squaresausage/Open-Source-PC110/optical/layers/README.md

## Layer Stack

BC2  -- Bottom Layer

BC1

IP2  -- Ground Layer

IC4

IC3

IC2

IC1

IP1 -- Power Layer

FC1

FC2 -- Top Layer

Link to high res pictures: https://drive.google.com/drive/folders/1oFIpbjULZVqb537QuhwhyOqd0YHSsCfh?usp=sharing
