squaresausage/Open-Source-PC110/PCB/Mainboard/README.md

### IBM PC110 PCB redesigned in KiCad

Layer Stack-up

| Index | Layer name | Description  |
| ----- | --- | --- |
| 1 | FC2 | Top |
| 2 | FC1 | Signal |
| 3 | IP1 | Power |
| 4 | IC1 | Signal |
| 5 | IC2 | Signal |
| 6 | IC3 | Signal |
| 7 | IC4 | Signal |
| 8 | IP2 | Ground |
| 9 | BC1 | Signal |
| 10 | BC2 | Bottom |

Here is a render of FC1, IC1, IC2, IC3, IC4 and BC1 together:

Screenshot 2025-01-25 at 10 13 16 PM

And here is a render of FC2, FC1, IC1, IC2, IC3, IC4, BC1 and BC2 together:
Screenshot 2025-02-05 at 3 54 23 PM

And here are 3D renders from the top and bottom layers:

Top side:

Real picture:



3D render:

Screenshot 2025-03-01 at 7 24 52 AM

Bottom side:

Real picture:



3D render:

Screenshot 2025-03-01 at 8 22 09 AM

Schematic Organization
-----
Here is a view of the schematic hierarchy:

Screenshot 2025-06-28 at 11 49 18 PM

Description of each schematic sheet

| Page | Sheet Name | Description  |
| ---- | --- | --- |
| 1 | Root | Index of all sheets  |
| 2 | Clock | Local Oscillator and Clock Distribution Tree |
| 3 | Processor  | CPU and Debug pins |
| 4 | Chipset  | SCAMP IV chipset North Bridge |
| 5 | VGA | Video Controller and Video RAM |
| 6 | Memory  | Internal Memory Back and RAM Expansion Connector |
| 7 | ROM | BIOS and Font Maskrom |
| 8 | ASIC | Bowman and Pluto, South Bridge |
| 9 | Super IO | FDD, Parallel and Serial ports |
| 10 | Power | Power Controller, PSU Connector, Status LCD, and Touchpad |
| 11 | PCMICA  | PCMCIA Controller and Related Power Controller |
| 12 | Audio | Sound Controller, FM Synthesizer and related analogue AMP |
| 13 | Storage | Internal Flash memory, CF card interface |
| 14 | Keyboard | Keyboard controller, Trackpoint controller |
| 15 | Docking | Docking Station, Internal Modem Connector |

Combined Schematic on one page
-----
Here is a combined schematic on a single page, just for the appreciation of its complexity.

PC110-Singlesheet-Schematic

Aside from the fun aspect of combining all the sheets on a single one, there is a practical use that is related to the recreation of the schematic from a given PCB. On KiCad, you cannot select components from different sheets simultaneously. Therefore, you cannot highlight all the components on your schematic at once to see if there is still any component on the layout that is not mapped. However, with a single sheet compilation, you can do that (as it is shown below) and you can go back to the layout and see if there is still any component that is left behind. Below you can see that, on the layout for both top and bottom layers, all the components are highlighted.

All components selected on the schematic

Screenshot 2025-07-19 at 1 20 59 PM

Highlighted components on the top layer



Highlighted components on the bottom layer



And here is the SVG version of the single-sheet 

PC110-Singlesheet-Schematic

PCB statistics report
=====================

Board
-----
- Width: 150.0500 mm
- Height: 107.3513 mm
- Area: 12400.2967 mm²

Pads
----
- Through hole: 29
- SMD: 4860
- Total: 4889

Vias
----
- Through vias: 2407
- Blind/buried: 3684
- Total: 6091

Components
----------

| | Front Side | Back Side | Total |
|---|---|---|---|
|THT: | 1 | 0 | 1 |
|SMD: | 486 | 446 | 932 |
|Unspecified:  | 0 | 1 | 1 |
|Total: | 487 | 447 | 934 |

Drill holes
-----------

| Count | Shape | X Size | Y Size | Plated | Via/Pad | Start Layer | Stop Layer |
|---|---|---|---|---|---|---|---|
|  1950 | Round | 0.2000 mm | 0.2000 mm | PTH | Via | BC1 | BC2 |
|  1914 | Round | 0.2000 mm | 0.2000 mm | PTH | Via | FC2 | BC2 |
|  1730 | Round | 0.2000 mm | 0.2000 mm | PTH | Via | FC2 | FC1 |
| 493 | Round | 0.3000 mm | 0.3000 mm | PTH | Via | FC2 | BC2 |
| 20 | Round | 0.8000 mm | 0.8000 mm | PTH | Pad | FC2 | BC2 |
| 5 | Round | 1.0000 mm | 1.0000 mm | PTH | Pad | FC2 | BC2 |
| 2 |  Slot | 2.0000 mm | 0.9000 mm | PTH | Pad | FC2 | BC2 |
| 2 |  Slot | 0.8000 mm | 2.2000 mm | PTH | Pad | FC2 | BC2 |
| 2 | Round | 0.2000 mm | 0.2000 mm | PTH | Via | FC2 | IC2 |
| 1 | Round | 0.2000 mm | 0.2000 mm | PTH | Via | FC2 | IC1 |
| 1 | Round | 0.3000 mm | 0.3000 mm | PTH | Via | BC1 | BC2 |
| 1 | Round | 0.2000 mm | 0.2000 mm | PTH | Via | IP1 | BC2 |

Here is a cross section of the PCB stack-up

Board_cross_section
