squaresausage/Open-Source-PC110/Modifications/Altium/README.md

Here you can find the PCB projects converted from KiCad to Altium to bring more versatility and make Altium's special offerings available to this project.
