squaresausage/Open-Source-PC110/Modifications/PC110-ITX-all-in-one/README.md

## PC110-ITX all-in-one

This is an effort to build an ITX form factor motherboard with all the PC110 components, the docking station as the PSU board all blended.
