squaresausage/Open-Source-PC110/Modifications/PC110-ITX/README.md

## PC110-ITX Form Factor

This is an effort to build an ITX form factor motherboard with all the PC110 components, but the BGA parts have been converted to QFP alternatives.

Here is how the netlist looked before the placement.

Screenshot 2025-07-03 at 5 40 27 PM

And here is when the placement has been performed.

Screenshot 2025-07-03 at 6 51 45 PM

Also, here is a 3D render of the board.

Screenshot 2025-07-03 at 6 53 05 PM
