squaresausage/Open-Source-PC110/Modifications/RAS4/README.md

## Using RAS4 to add extra 4MB to the internal RAM

VL_D12 is now labled as RAS#4 on the schematic

Screenshot 2025-06-20 at 5 41 18 AM

Screenshot 2025-06-20 at 5 41 07 AM
