squaresausage/Open-Source-PC110/PCB/RAM-16MB/README.md

## 16MB RAM Module PCB

Layer Stack-up

| Index | Layer name | Description  |
| ----- | --- | --- |
| 1 | FC | Top |
| 2 | IP1 | Power |
| 3 | IP2 | Ground |
| 4 | BC | Bottom |

Here is a rendering of FC, IP1, IP2 and BC:

Screenshot 2025-03-25 at 2 49 15 AM

Here are renderings of the 3D model of the Docking Station PCB

Screenshot 2025-03-26 at 7 45 36 PM

Screenshot 2025-03-26 at 7 45 54 PM

PCB statistics report
=====================
- Date: Tuesday, March 25, 2025 at 03:06:19 AM
- Project: RAM-Module
- Board name: RAM-Module

Board
-----
- Width: 41.4600 mm
- Height: 41.6000 mm
- Area: 1724.3156 mm²
- Thickness: 0.6mm

Pads
----
- Through hole: 0
- SMD: 312
- Connector: 0
- NPTH: 0

Vias
----
- Through vias: 152
- Blind/buried: 0
- Micro vias: 0

Components
----------

| | Front Side | Back Side | Total |
|---|---|---|---|
|THT: | 0 | 0 | 0 |
|SMD: | 17 | 4 | 21 |
|Unspecified:  | 0 | 1 | 1 |
|Total: | 17 | 5 | 22 |

Drill holes
-----------

| Count | Shape | X Size | Y Size | Plated | Via/Pad | Start Layer | Stop Layer |
|---|---|---|---|---|---|---|---|
| 152 | Round | 0.3000 mm | 0.3000 mm | PTH | Via | FC | BC |
