squaresausage/Open-Source-PC110/PCB/Modem/README.md

## Here is the PCB Layout for the Modem Board

Layer Stack-up

| Index | Layer name | Description  |
| ----- | --- | --- |
| 1 | FC | Top |
| 2 | IC1 | Signal |
| 4 | IP1 | Power |
| 3 | IP2 | Power |
| 4 | IC2 | Signal |
| 4 | BC | Bottom |

Here is a render of FC, IC1, IP1, IP2, IC2 and BC:

Screenshot 2025-03-21 at 8 33 39 PM

Here are the 3D renders from the board:

Screenshot 2025-03-21 at 8 27 20 PM

Screenshot 2025-03-25 at 2 58 01 AM

PCB statistics report
=====================
- Date: Friday, March 21, 2025 at 08:35:15 PM
- Project: Modem
- Board name: Modem

Board
-----
- Width: 64.6100 mm
- Height: 58.9100 mm
- Area: 3494.8376 mm²

Pads
----
- Through hole: 23
- SMD: 735
- Connector: 0
- NPTH: 0

Vias
----
- Through vias: 344
- Blind/buried: 0
- Micro vias: 0

Components
----------

| | Front Side | Back Side | Total |
|---|---|---|---|
|THT: | 0 | 0 | 0 |
|SMD: | 75 | 136 | 211 |
|Unspecified:  | 0 | 0 | 0 |
|Total: | 75 | 136 | 211 |

Drill holes
-----------

| Count | Shape | X Size | Y Size | Plated | Via/Pad | Start Layer | Stop Layer |
|---|---|---|---|---|---|---|---|
| 344 | Round | 0.3000 mm | 0.3000 mm | PTH | Via | FC | BC |
| 18 | Round | 1.0000 mm | 1.0000 mm | PTH | Pad | FC | BC |
| 5 | Round | 1.2000 mm | 1.2000 mm | PTH | Pad | FC | BC |
