squaresausage/Open-Source-PC110/Flash/EN29F040A/README.md

## Flash dump from the EN29FF040A from the Modem board
