squaresausage/Open-Source-PC110/PCB/DockingStation/README.md

## Docking Station PCB

Layer Stack-up

| Index | Layer name | Description  |
| ----- | --- | --- |
| 1 | FC | Top |
| 2 | IP1 | Ground |
| 3 | IP2 | Power |
| 4 | BC | Bottom |

Here is a rendering of FC, IP1, IP2 and BC:

Screenshot 2025-03-18 at 2 07 06 PM

Here are renderings of the 3D model of the Docking Station PCB

Screenshot 2025-03-18 at 2 07 46 PM

Screenshot 2025-03-18 at 2 08 01 PM
