squaresausage/Open-Source-PC110/PCB/PSU/README.md

## Here is the PCB Layout for the PSU board

Layer Stack-up

| Index | Layer name | Description  |
| ----- | --- | --- |
| 1 | FC | Top |
| 2 | IC | Signal |
| 3 | IP | Ground |
| 4 | BC | Bottom |

Here is a render of FC, IC, IP and BC:

Screenshot 2025-03-15 at 6 35 28 PM

Here are 3D models of the PSU board:

Screenshot 2025-03-15 at 6 34 14 PM

Screenshot 2025-03-15 at 6 34 32 PM

PCB statistics report
=====================
- Date: Saturday, March 15, 2025 at 01:16:45 PM
- Project: PSU
- Board name: PSU

Board
-----
- Width: 72.3100 mm
- Height: 44.9600 mm
- Area: 2701.6649 mm²

Pads
----
- Through hole: 20
- SMD: 688
- Connector: 0
- NPTH: 0

Vias
----
- Through vias: 212
- Blind/buried: 0
- Micro vias: 0

Components
----------

| | Front Side | Back Side | Total |
|---|---|---|---|
|THT: | 0 | 10 | 10 |
|SMD: | 171 | 76 | 247 |
|Unspecified:  | 1 | 0 | 1 |
|Total: | 172 | 86 | 258 |

Drill holes
-----------

| Count | Shape | X Size | Y Size | Plated | Via/Pad | Start Layer | Stop Layer |
|---|---|---|---|---|---|---|---|
| 203 | Round | 0.3000 mm | 0.3000 mm | PTH | Via | FC | BC |
| 14 | Round | 0.8000 mm | 0.8000 mm | PTH | Pad | FC | BC |
| 6 | Round | 1.3000 mm | 1.3000 mm | PTH | Pad | FC | BC |
| 5 | Round | 0.8000 mm | 0.8000 mm | PTH | Via | FC | BC |
| 3 | Round | 0.6000 mm | 0.6000 mm | PTH | Via | FC | BC |
| 1 | Round | 1.0000 mm | 1.0000 mm | PTH | Via | FC | BC |
