squaresausage/Open-Source-PC110/Flash/OKI-MSM538032E/README.md

## OKI MSM538032E Memory dump

Here is a memory dump from the MSM538032E made by OKI.

You can use https://binvis.io/ to study the binary file.
In this analysis https://github.com/bbbradsmith/binxelview was used.

Here is how the chip was fitted on a proto board to be read by a programmer





And here are the results



It looks like the first 8k bytes are exposed in the "font window" and is a properly formatted option rom with the Japanese character sets.



This is what the 8k bytes look like:

WhatsApp Image 2025-03-04 at 20 44 57

Higher resolution character sets in their too.

Digging further in the code it seems that there is a reference to the different size character sets:
