squaresausage/Open-Source-PC110/datasheets/top/README.md

## parts on the top layer

tiplane
tiplane-1
