squaresausage/Open-Source-PC110/datasheets/bottom/README.md

## parts on the bottom later
teplane
teplane-1
