squaresausage/Open-Source-PC110/PCB/Mainboard/Single-Sheet-Schematic/README.md

Single Sheet Schematic

All the sheets were compiled into a single sheet
