squaresausage/Open-Source-PC110/PCB/Keyboard/Membrane/README.md

## IBM PC110 Keyboard Membrane

## Here is the PCB Layout for the PSU board

Layer Stack-up

| Index | Layer name | Description  |
| ----- | --- | --- |
| 1 | FC | Top |
| 1 | BC | Bottom |

Here is a render of FC and BC:

Screenshot 2025-03-25 at 11 03 26 PM

Here are 3D models of the Keyboard membrane:

Screenshot 2025-03-25 at 11 03 48 PM

Screenshot 2025-03-26 at 6 59 02 PM

These design files can be used to recreate the membrane from FlexPCB.
Additionally, their original membrane has been made using PET technology.
It can be built using PET technology. Here is an example of a vendor providing PET manufacturing service: 
https://www.pcbway.com/blog/Flexible_PCB/PET_7348f015.html
