squaresausage/Open-Source-PC110/datasheets/bottom/28F002 pinout.png

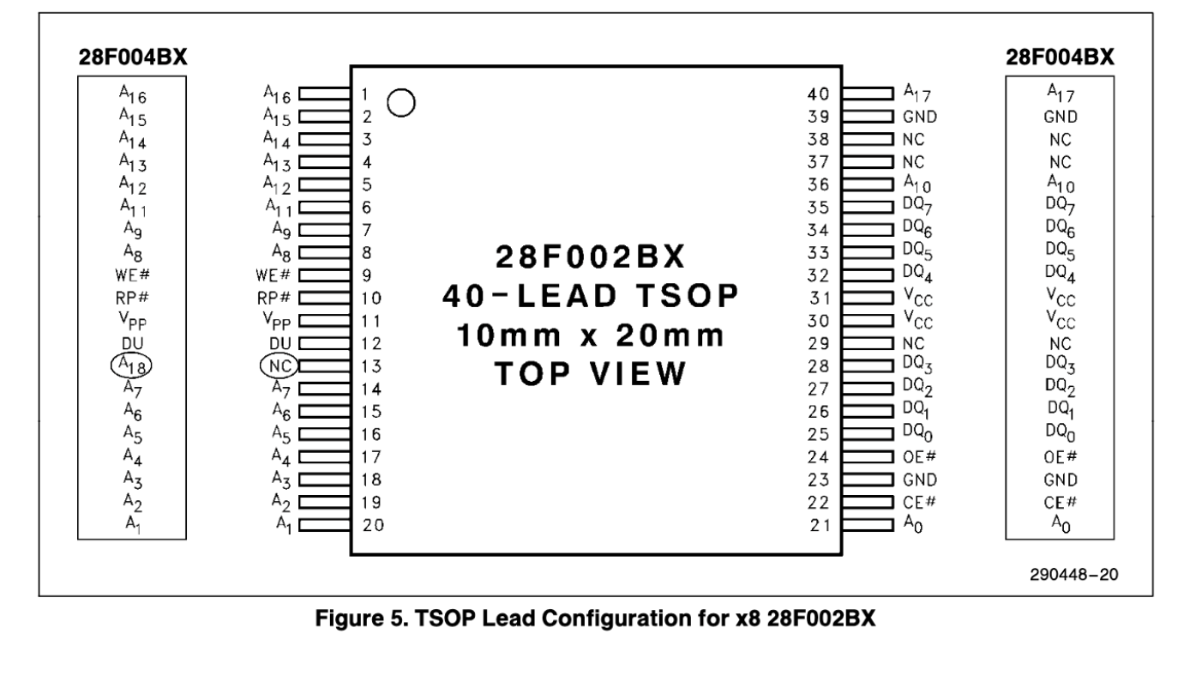
datasheets/bottom/28F002 pinout.png
