squaresausage/Open-Source-PC110/datasheets/bottom/AV9 pinout.png

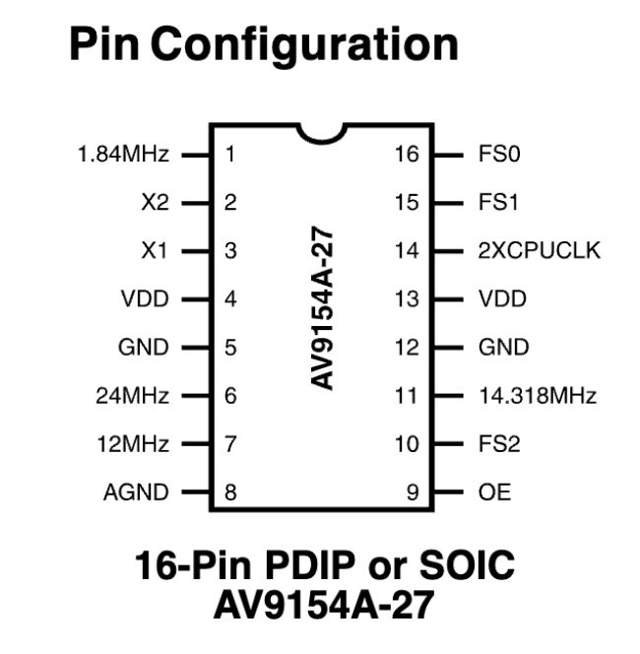
datasheets/bottom/AV9 pinout.png
