squaresausage/Open-Source-PC110/datasheets/bottom/D17137 pinout.png

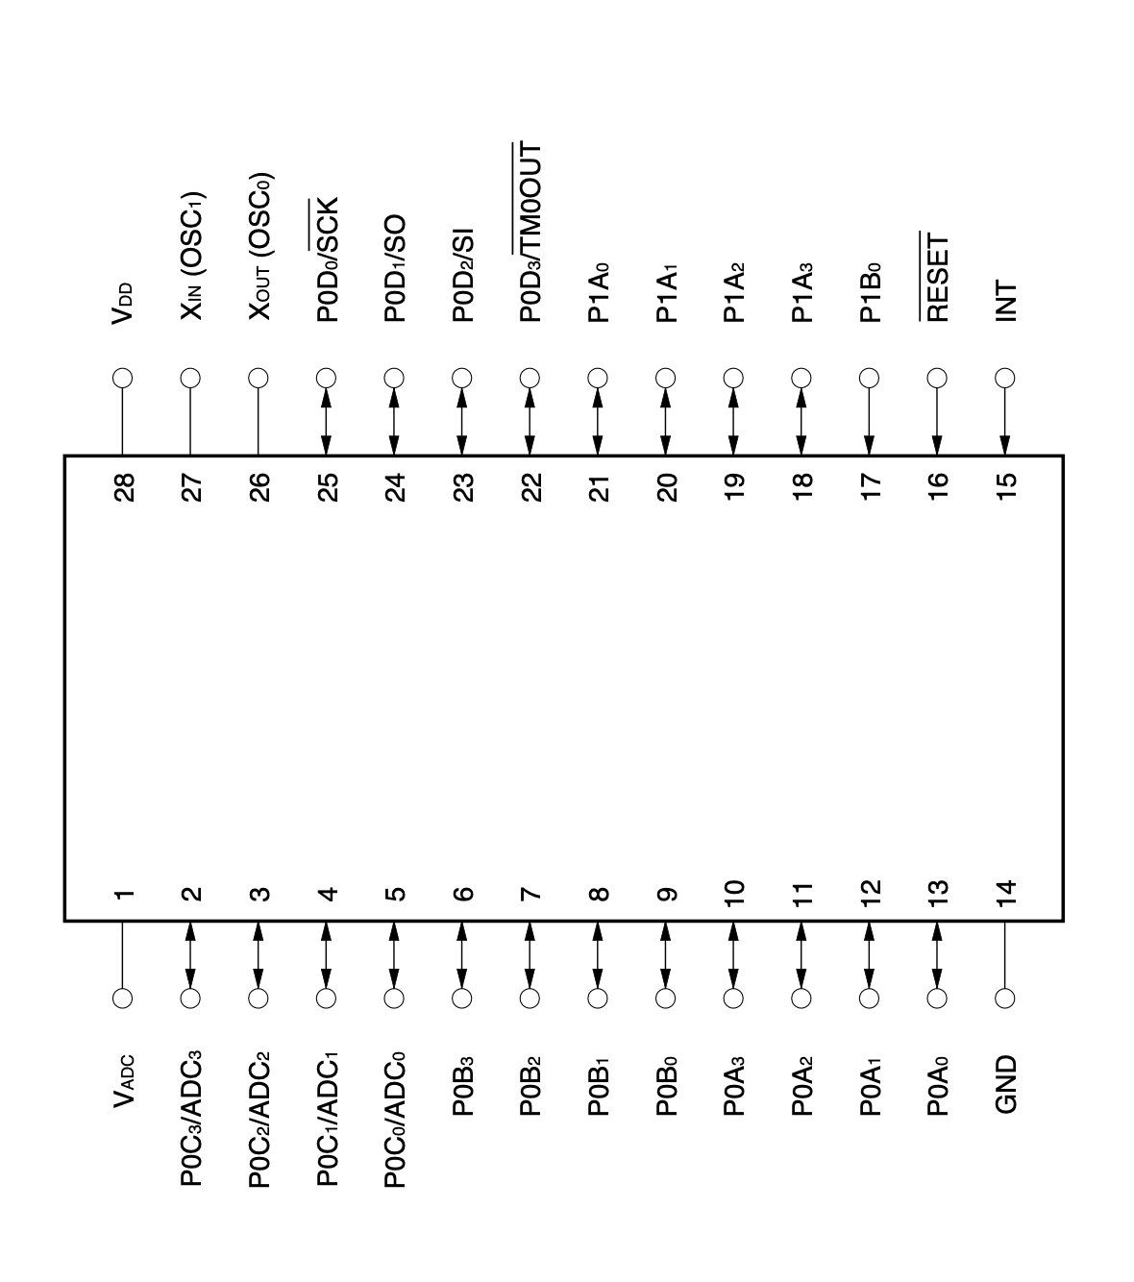
datasheets/bottom/D17137 pinout.png
