squaresausage/Open-Source-PC110/datasheets/bottom/F65535 BGA Ballmap.png

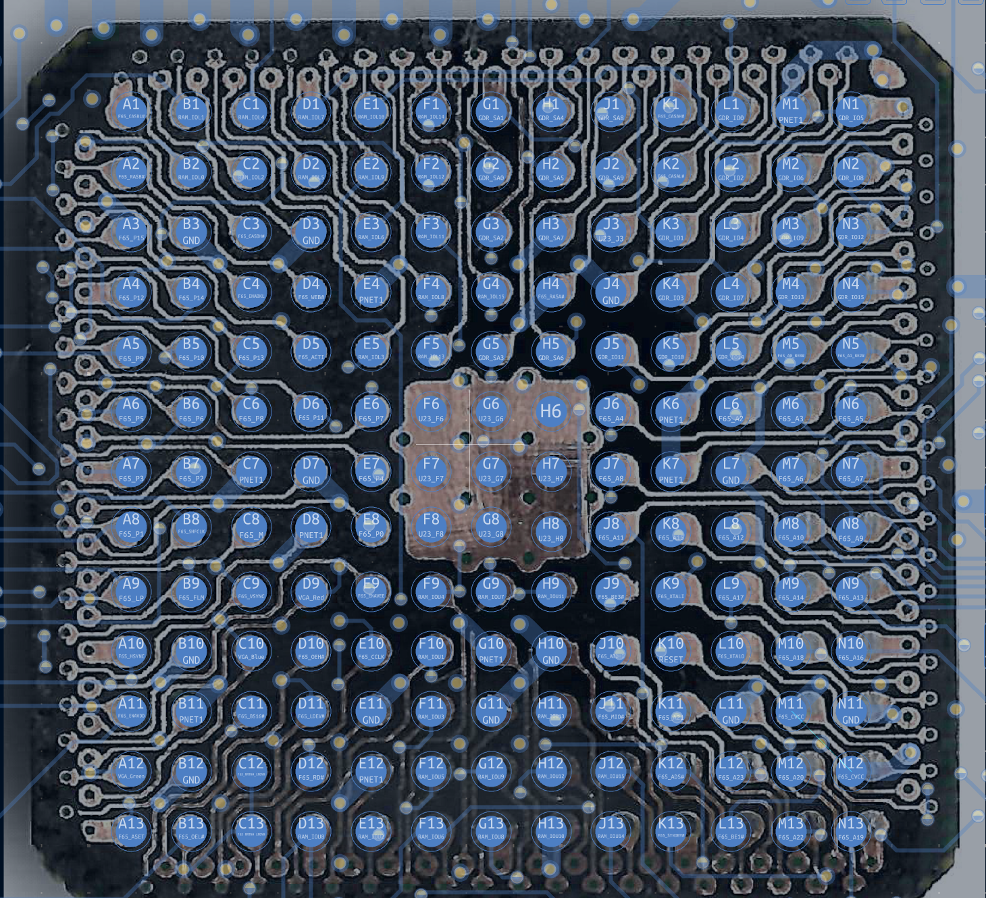
datasheets/bottom/F65535 BGA Ballmap.png
