squaresausage/Open-Source-PC110/datasheets/bottom/i486sx BGA ball map.png

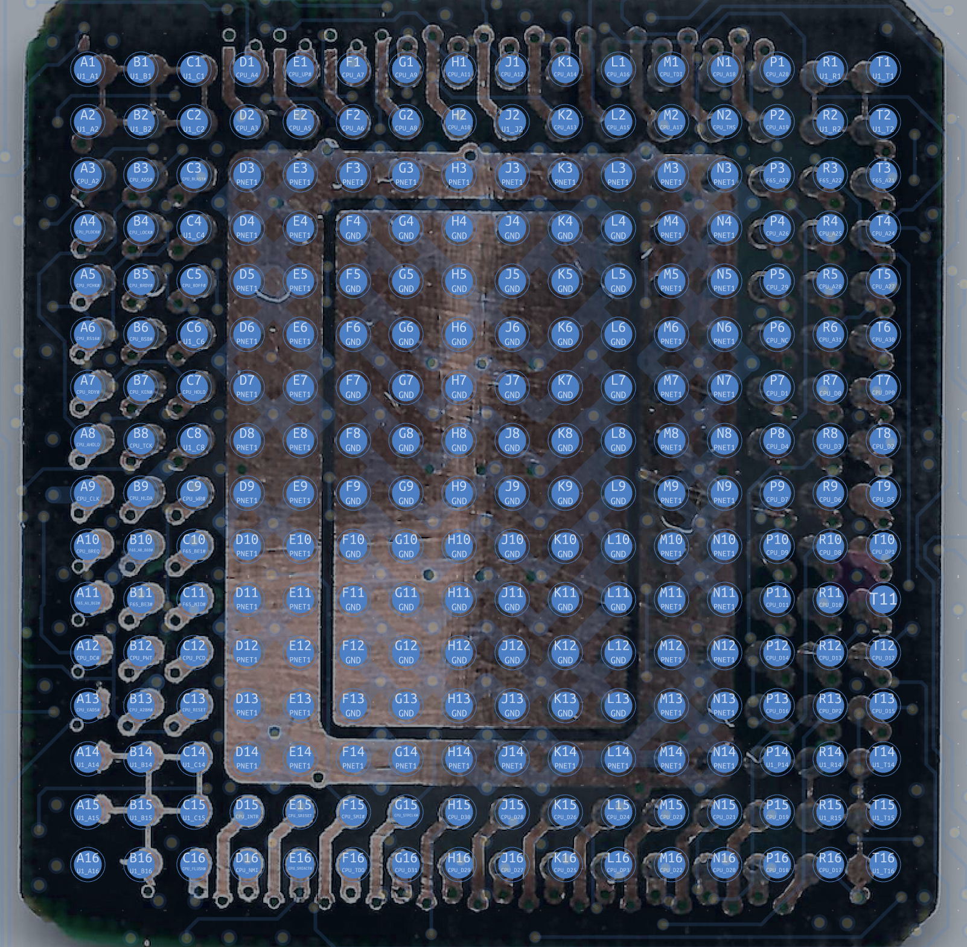
datasheets/bottom/i486sx BGA ball map.png
