squaresausage/Open-Source-PC110/datasheets/generic/connectors.jpg

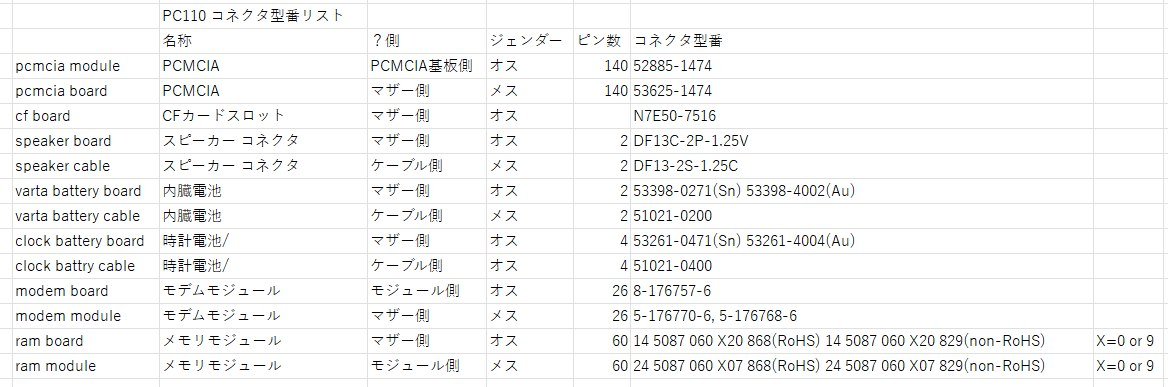
datasheets/generic/connectors.jpg
