squaresausage/Open-Source-PC110/datasheets/Modem/MN195001-pins.png

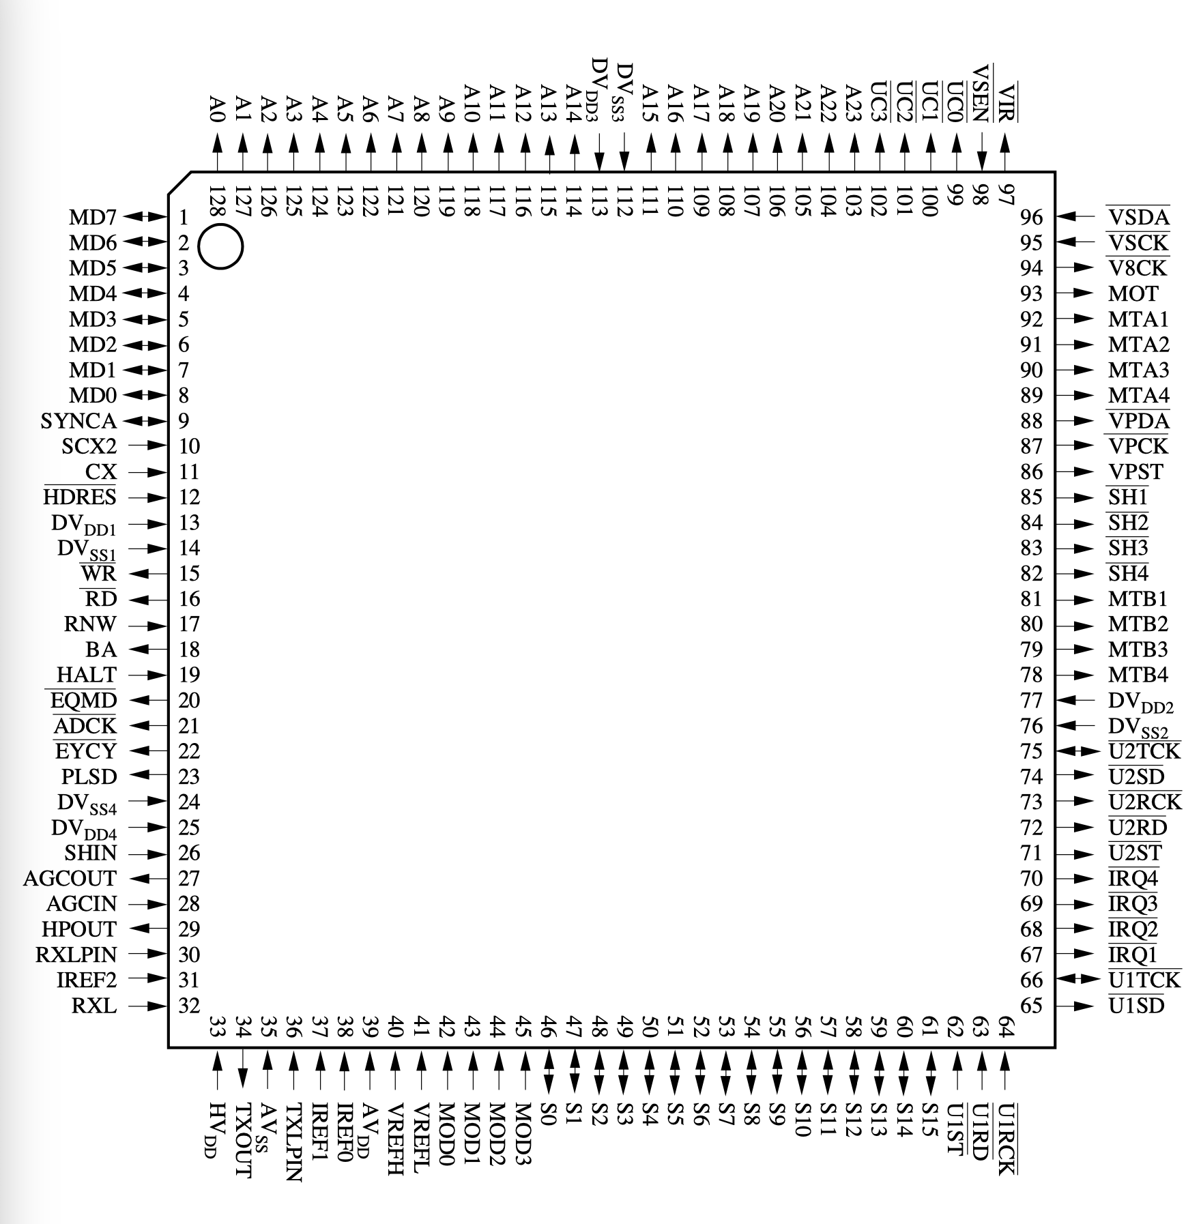
datasheets/Modem/MN195001-pins.png
