squaresausage/Open-Source-PC110/datasheets/top/15-m38.png

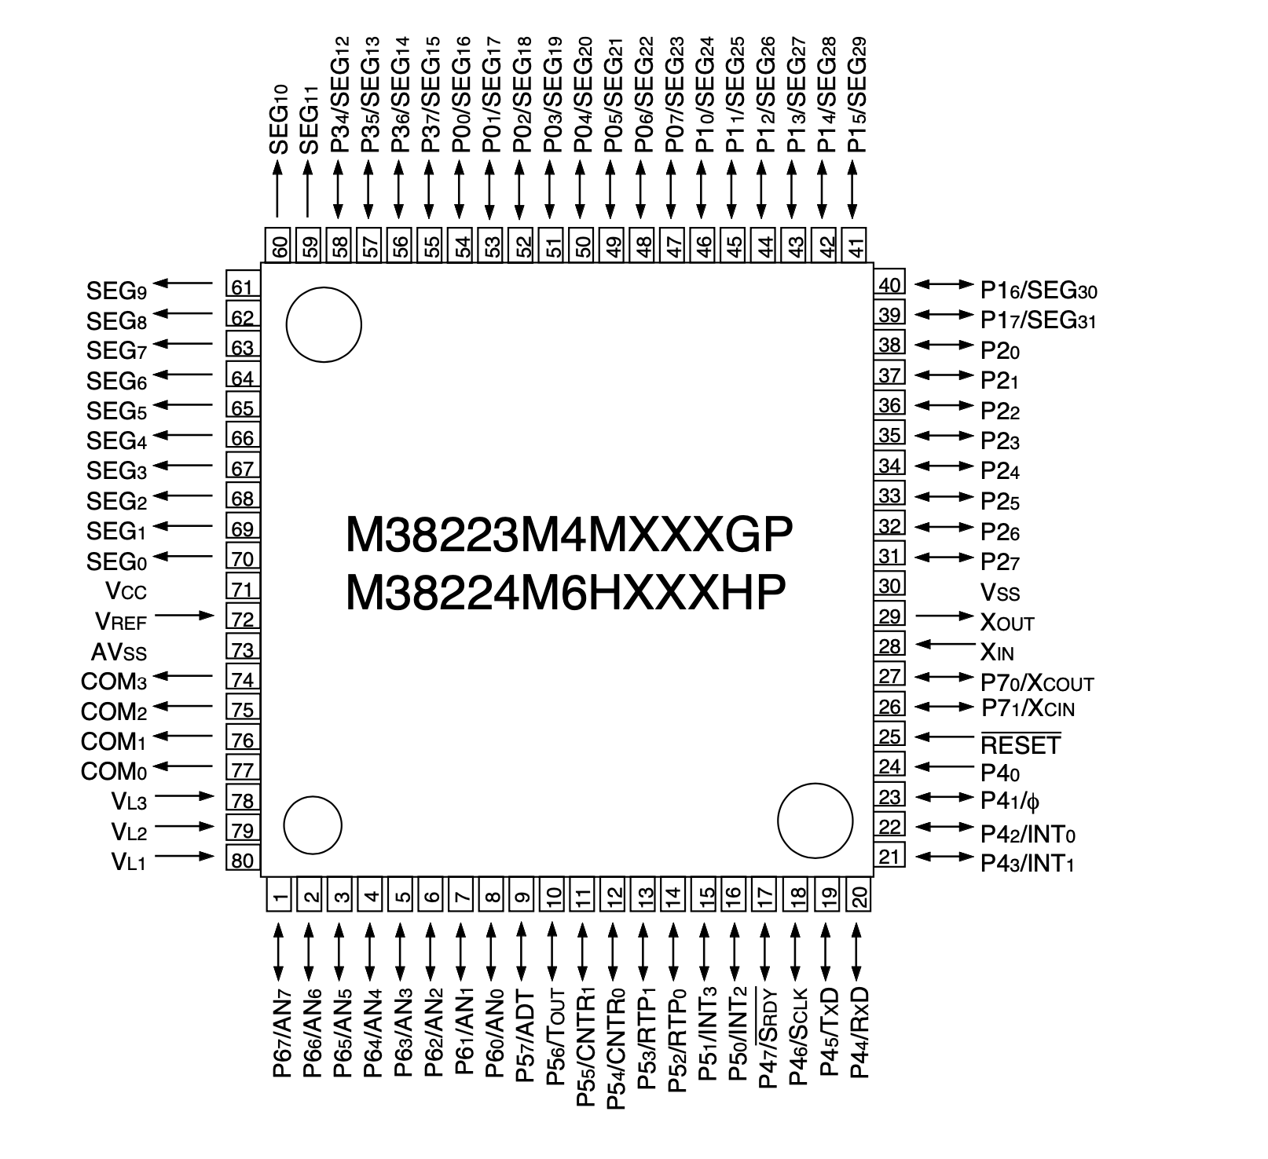
datasheets/top/15-m38.png
