squaresausage/Open-Source-PC110/datasheets/top/51w16160 pinout.png

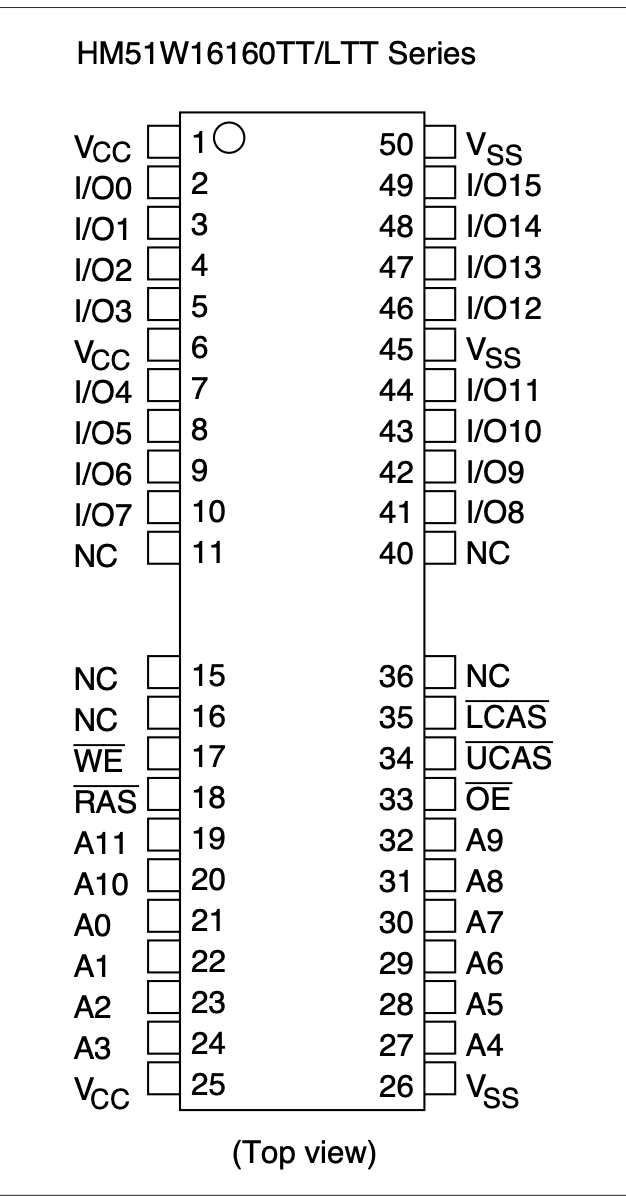
datasheets/top/51w16160 pinout.png
