squaresausage/Open-Source-PC110/datasheets/top/docking connector part.png

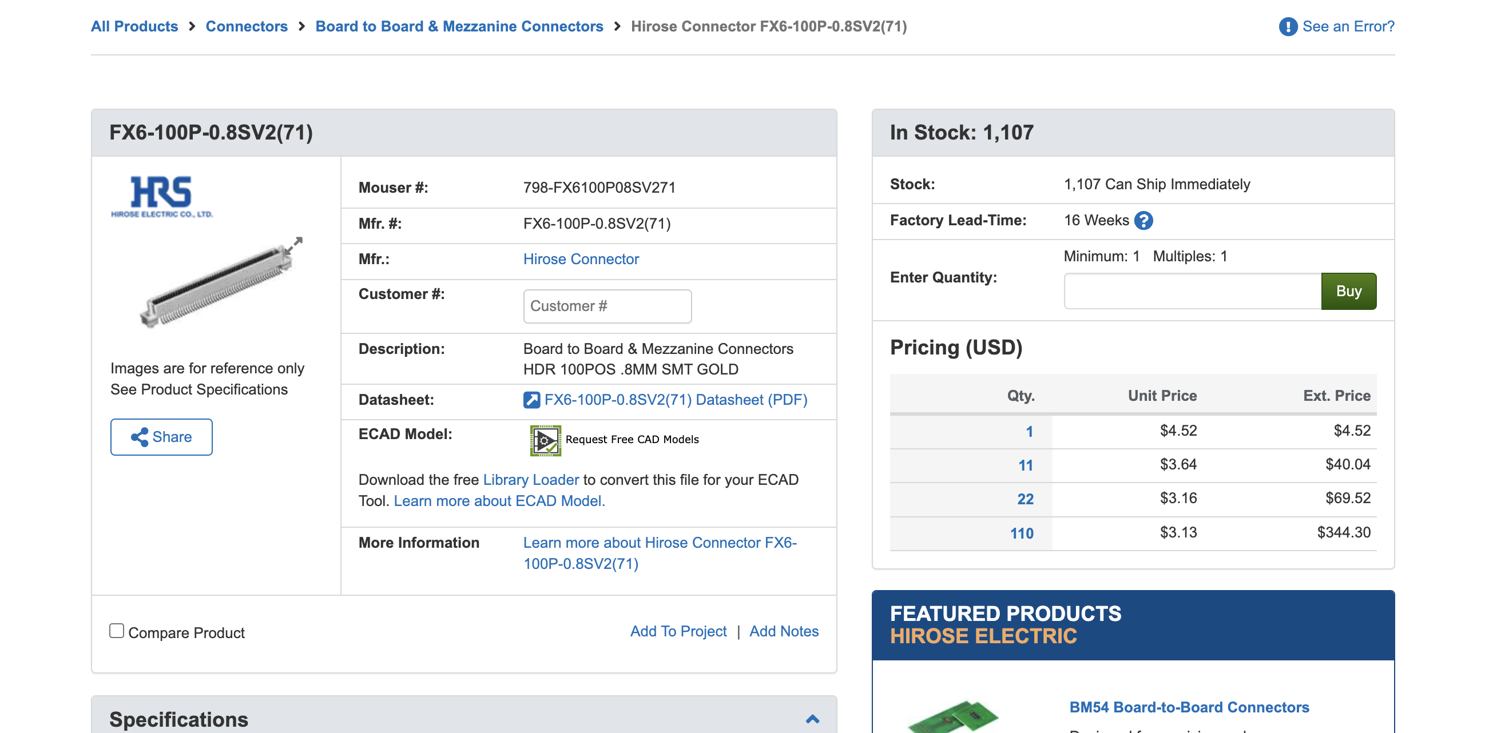
datasheets/top/docking connector part.png
