squaresausage/Open-Source-PC110/datasheets/top/docking pinout.jpg

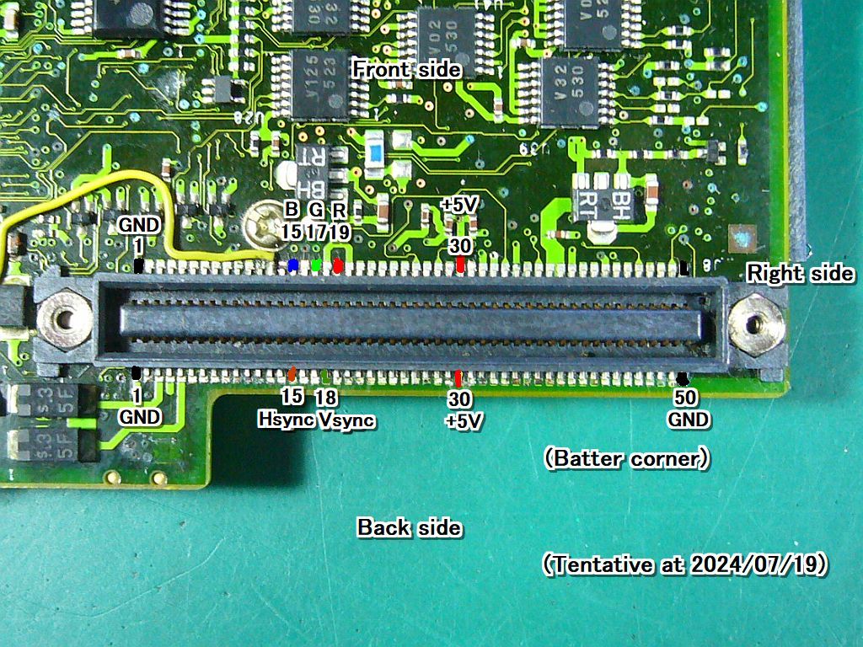
datasheets/top/docking pinout.jpg
