squaresausage/Open-Source-PC110/datasheets/top/LCD Connector.png

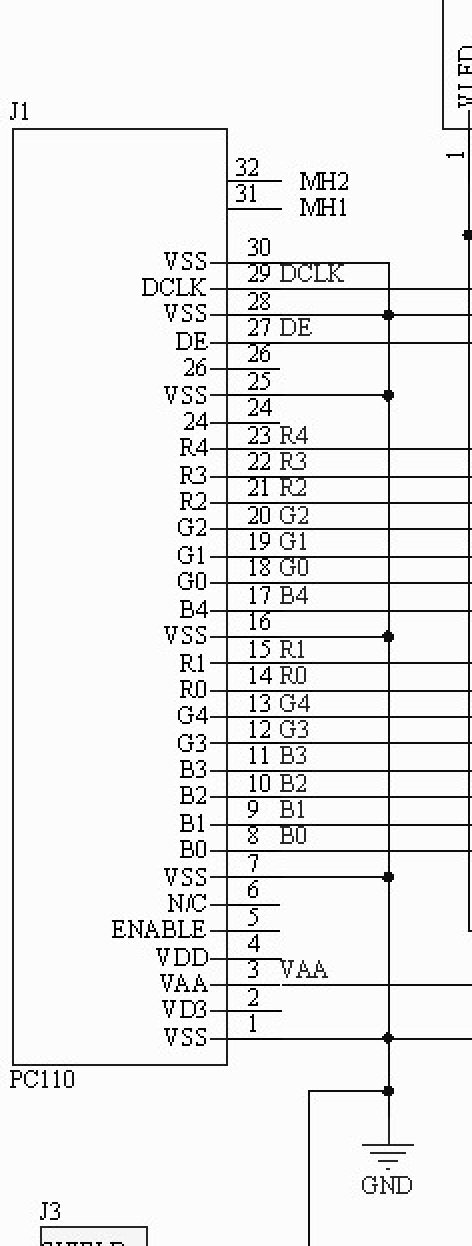
datasheets/top/LCD Connector.png
