squaresausage/Open-Source-PC110/datasheets/top/M538032C pinout.png

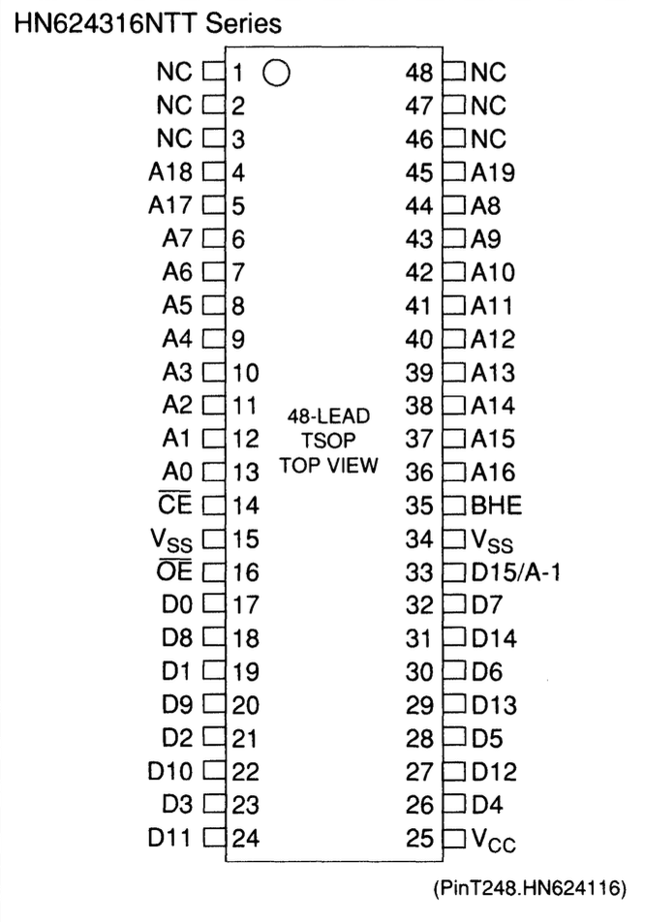
datasheets/top/M538032C pinout.png
