squaresausage/Open-Source-PC110/datasheets/top/MSM538032C pinout.png

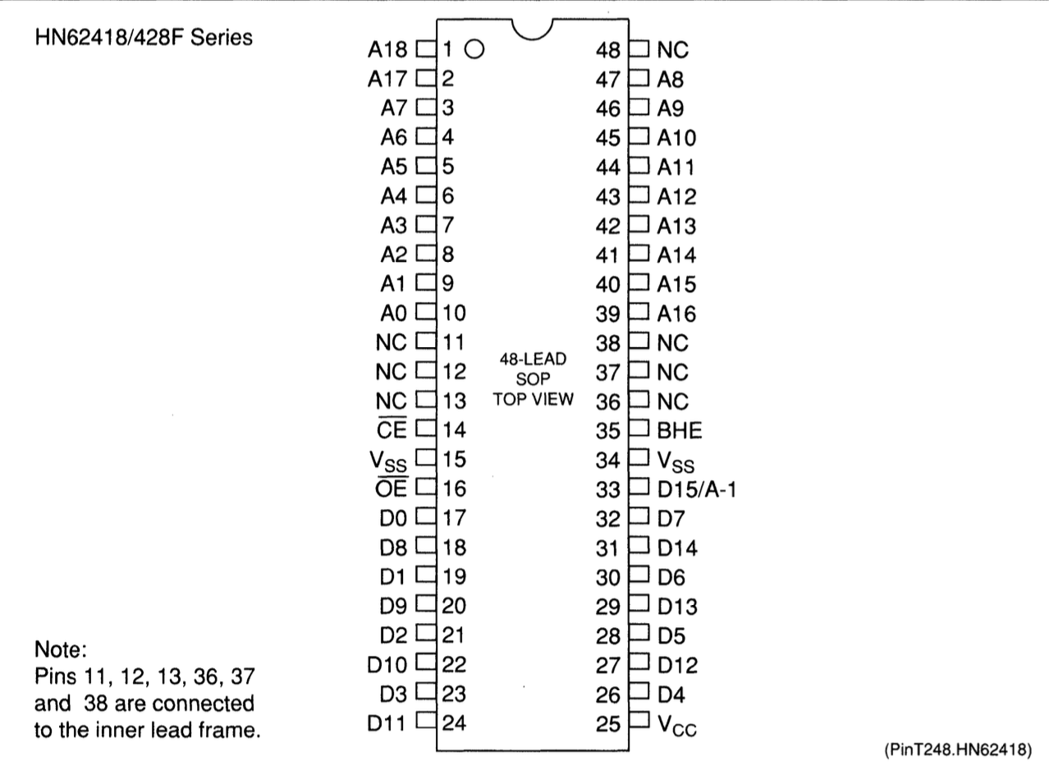
datasheets/top/MSM538032C pinout.png
