squaresausage/Open-Source-PC110/datasheets/top/power connector motherboard side part.png

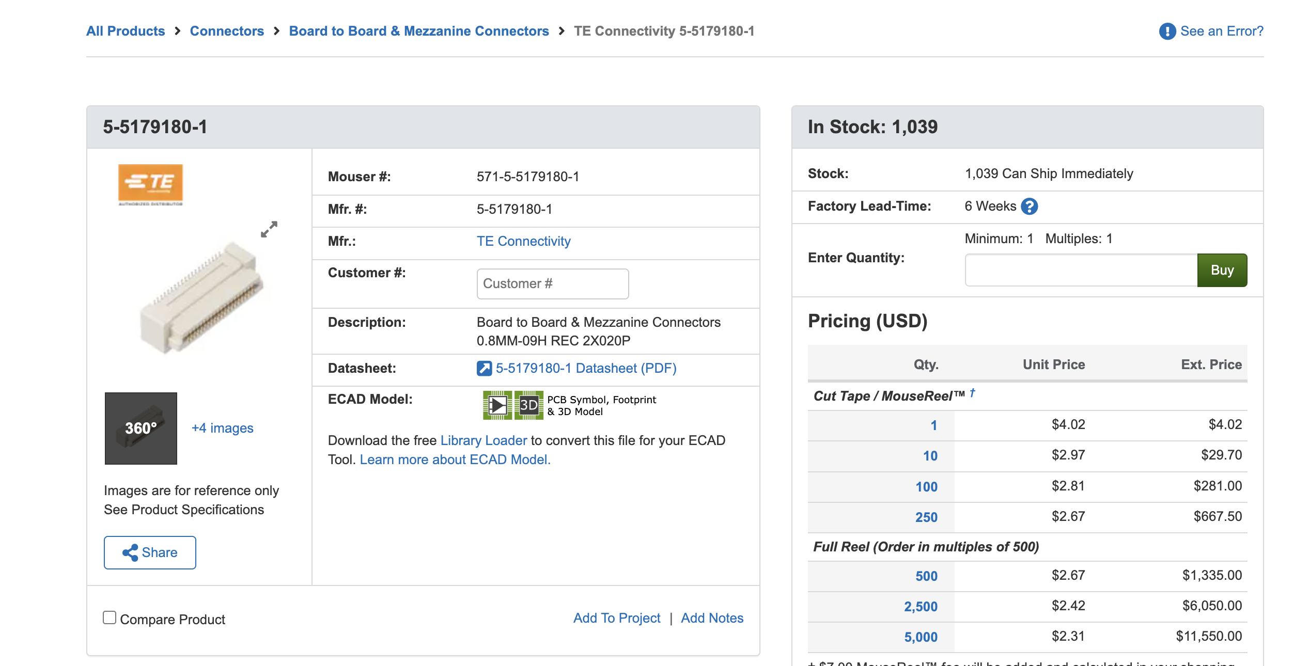
datasheets/top/power connector motherboard side part.png
