squaresausage/Open-Source-PC110/datasheets/top/power connector part.png

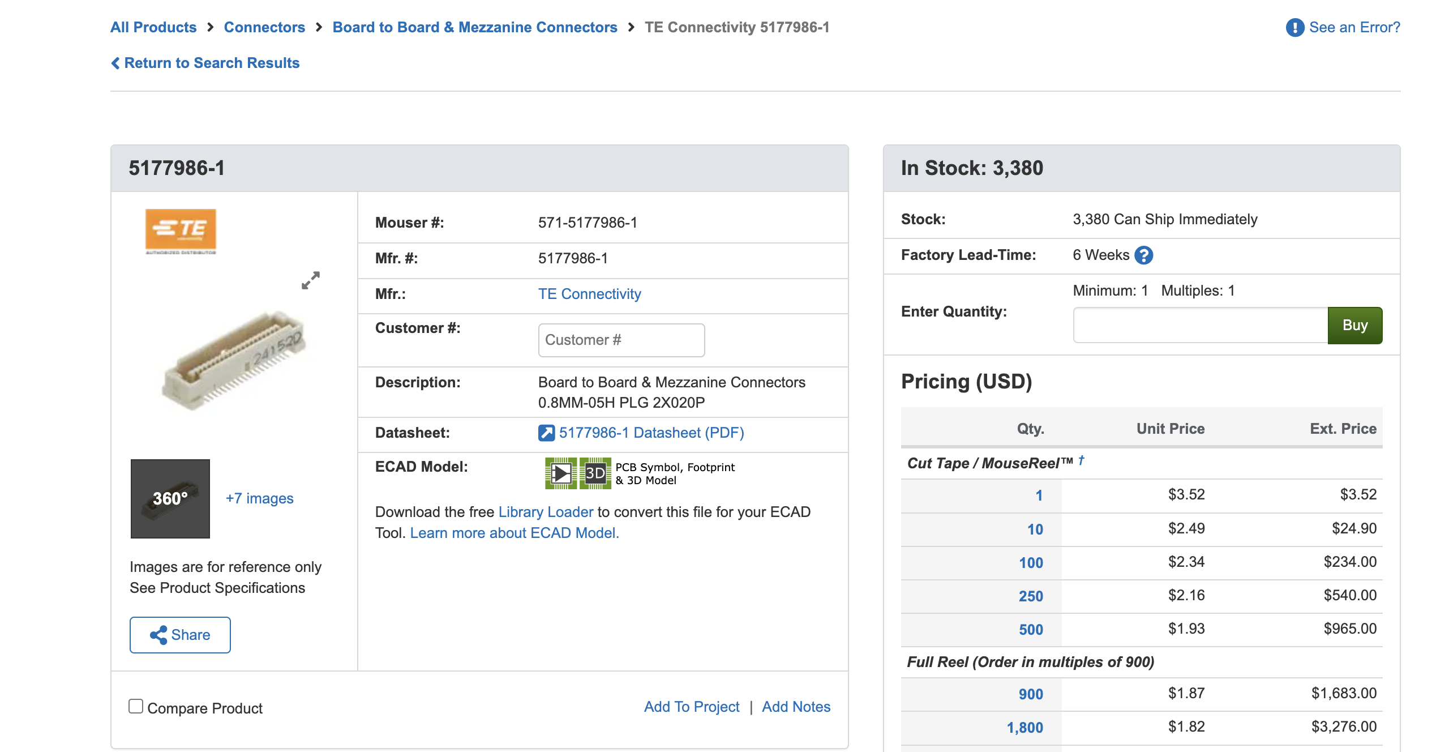
datasheets/top/power connector part.png
