squaresausage/Open-Source-PC110/datasheets/top/power connector.jpg

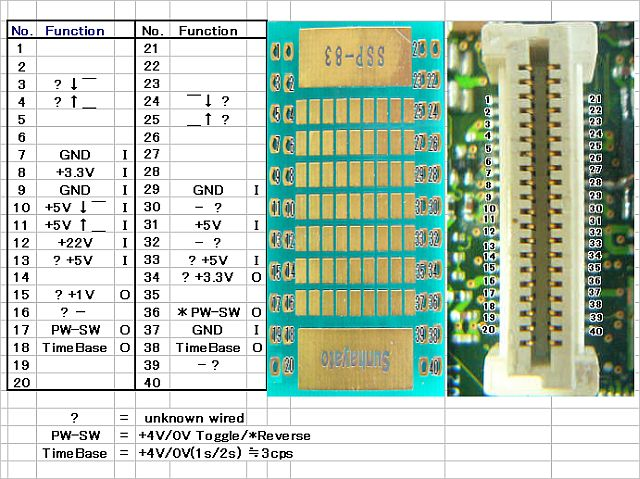
datasheets/top/power connector.jpg
