squaresausage/Open-Source-PC110/datasheets/top/RAM connector.jpg

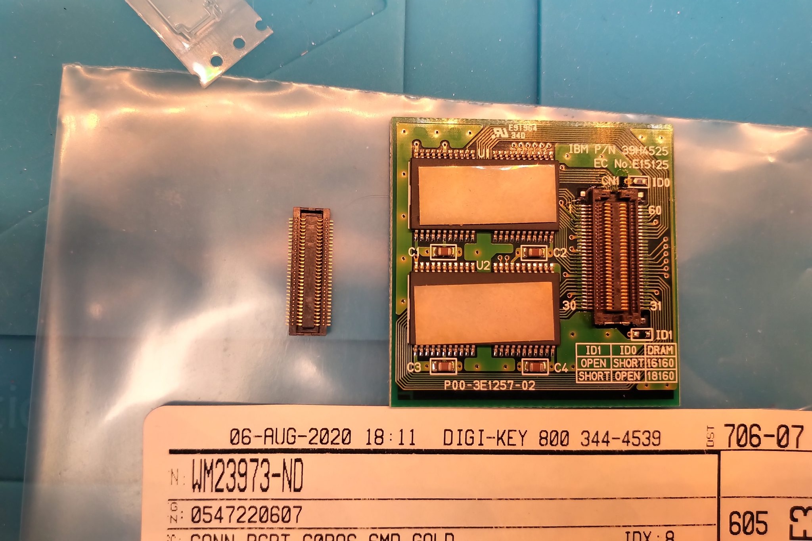
datasheets/top/RAM connector.jpg
