squaresausage/Open-Source-PC110/Modifications/RAS4/PHOTO-2025-06-20-01-07-58.jpg

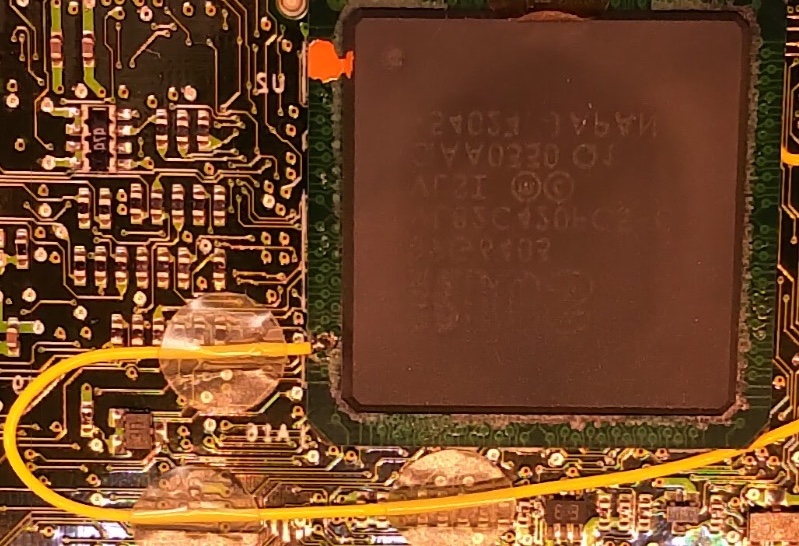
Modifications/RAS4/PHOTO-2025-06-20-01-07-58.jpg
