squaresausage/Open-Source-PC110/optical/16MB-RAM/back.jpeg

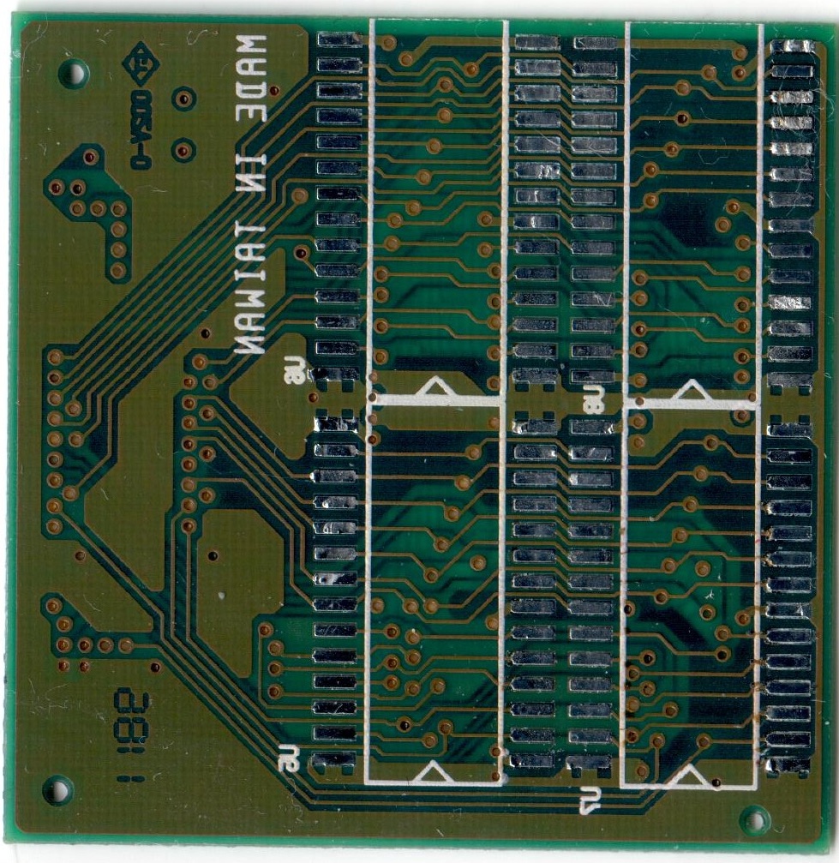
optical/16MB-RAM/back.jpeg
