squaresausage/Open-Source-PC110/optical/16MB-RAM/front.jpeg

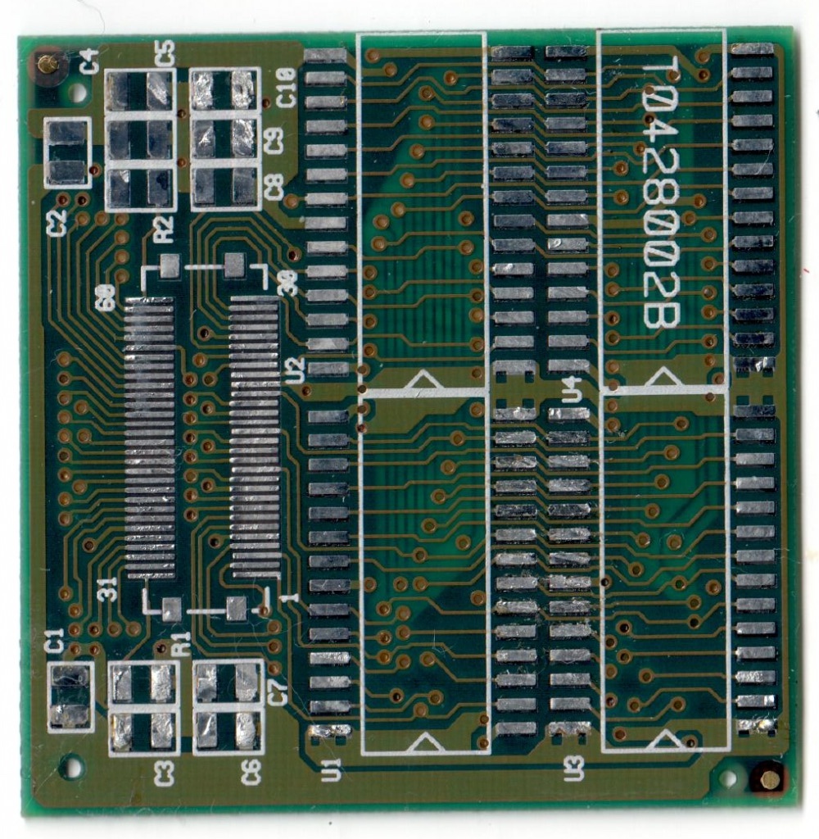
optical/16MB-RAM/front.jpeg
