squaresausage/Open-Source-PC110/optical/16MB-RAM/scan0001.jpg

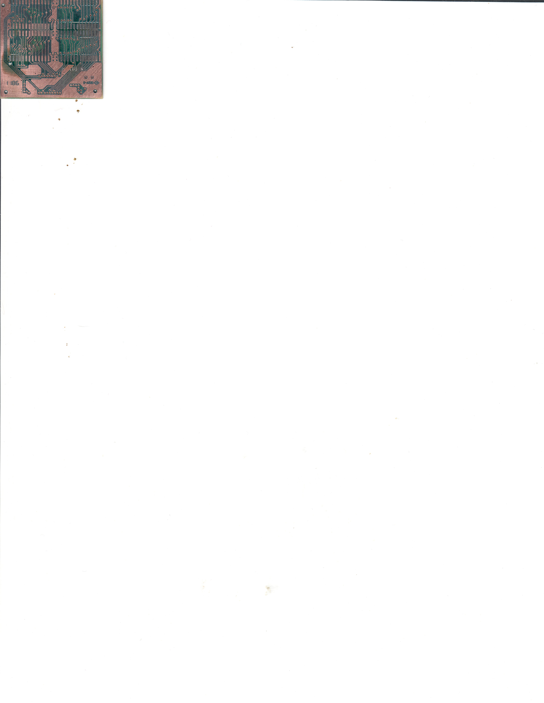
optical/16MB-RAM/scan0001.jpg
