squaresausage/Open-Source-PC110/optical/16MB-RAM/scan0003.jpg

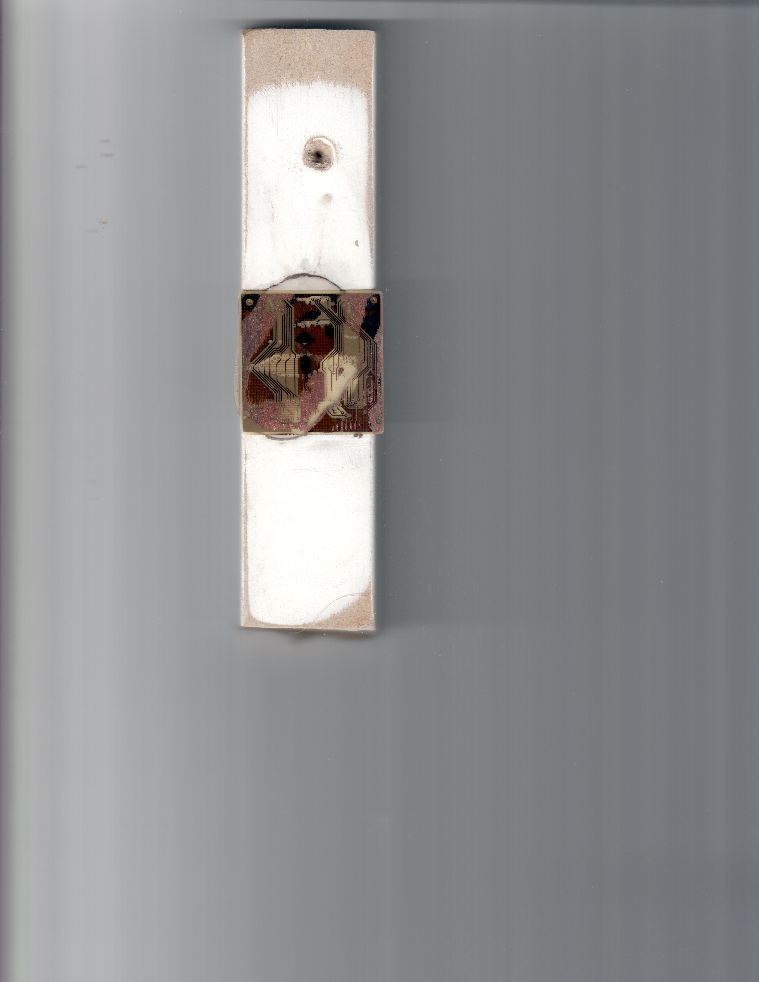
optical/16MB-RAM/scan0003.jpg
