squaresausage/Open-Source-PC110/optical/Chip Diagnostic/486sx BL.JPG

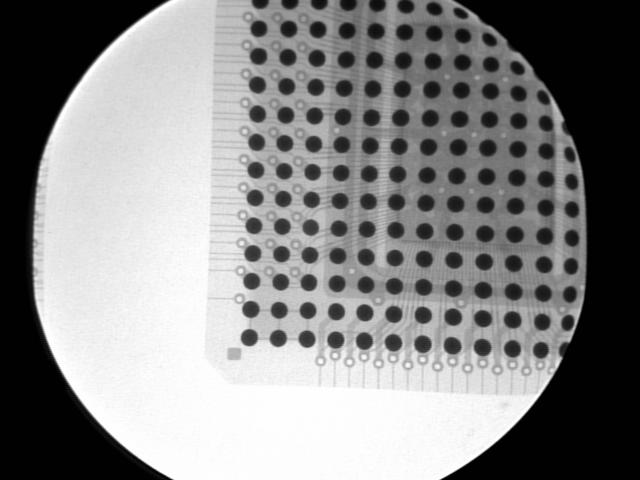
optical/Chip Diagnostic/486sx BL.JPG
