squaresausage/Open-Source-PC110/optical/Chip Diagnostic/486sx BR.JPG

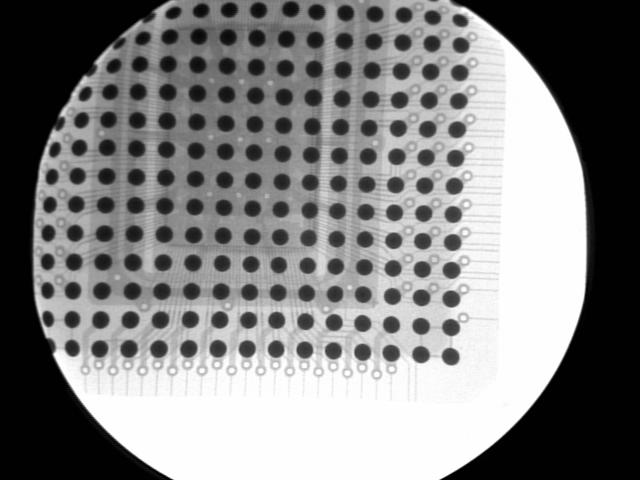
optical/Chip Diagnostic/486sx BR.JPG
