squaresausage/Open-Source-PC110/optical/Chip Diagnostic/486sx C.JPG

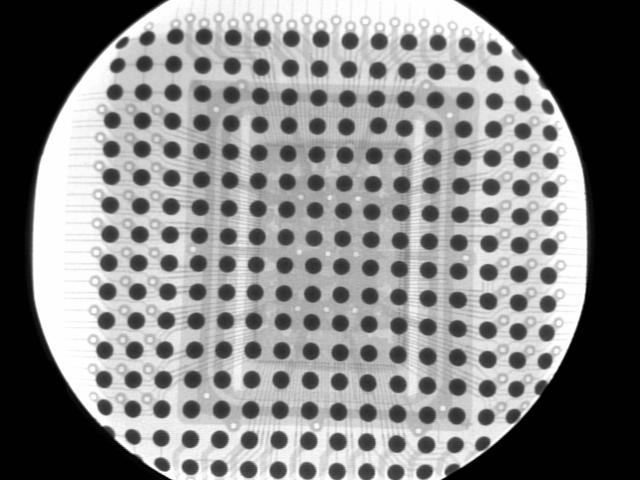
optical/Chip Diagnostic/486sx C.JPG
