squaresausage/Open-Source-PC110/optical/Chip Diagnostic/486sx TL.JPG

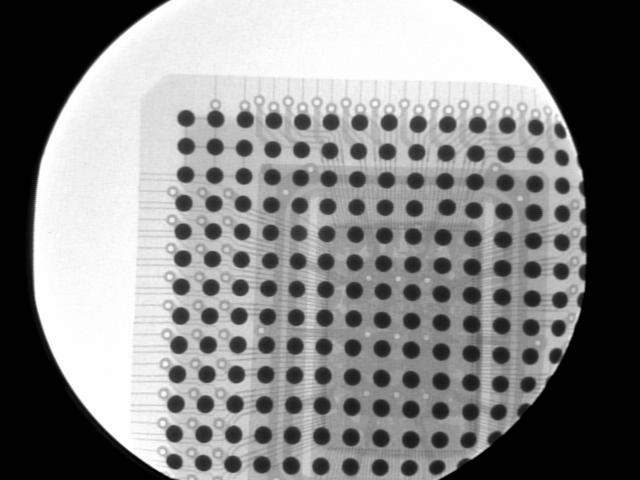
optical/Chip Diagnostic/486sx TL.JPG
