squaresausage/Open-Source-PC110/optical/Chip Diagnostic/486sx TR.JPG

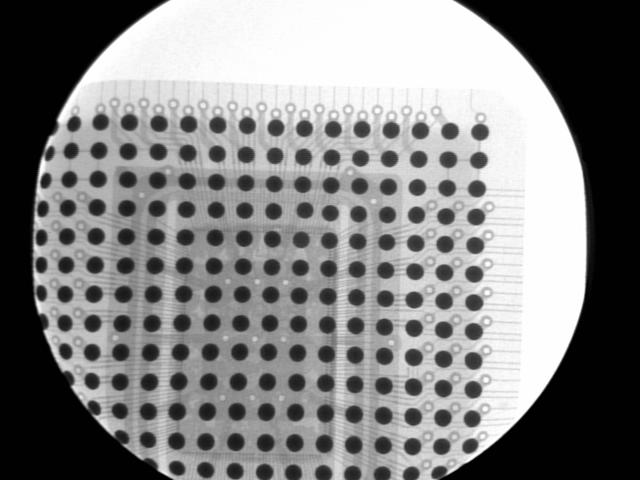
optical/Chip Diagnostic/486sx TR.JPG
