squaresausage/Open-Source-PC110/optical/Chip Diagnostic/Bowman.JPG

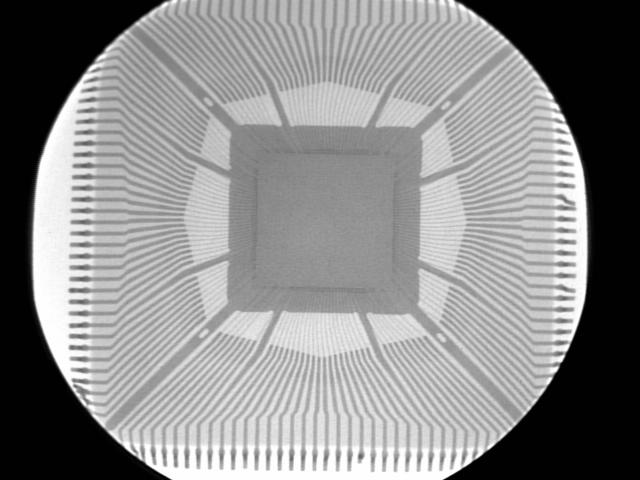
optical/Chip Diagnostic/Bowman.JPG
