squaresausage/Open-Source-PC110/optical/Chip Diagnostic/BRDDL.JPG

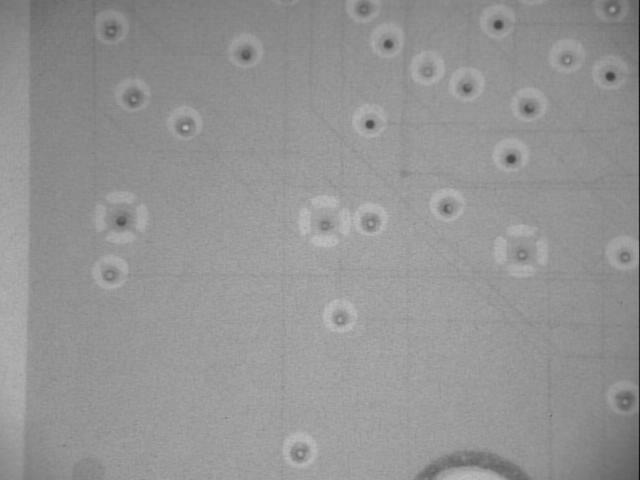
optical/Chip Diagnostic/BRDDL.JPG
