squaresausage/Open-Source-PC110/optical/Chip Diagnostic/BRDDR.JPG

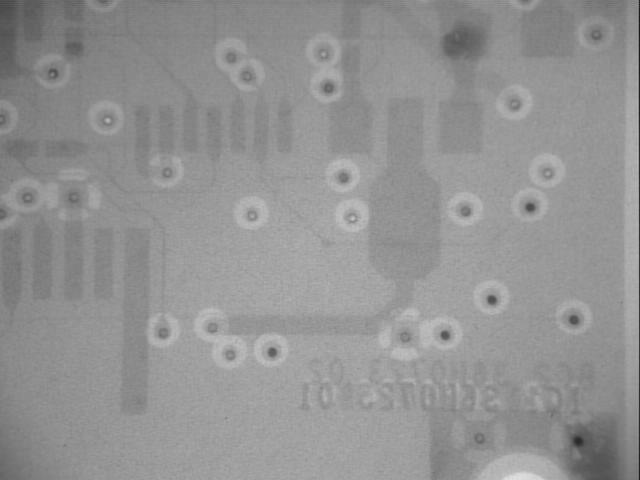
optical/Chip Diagnostic/BRDDR.JPG
