squaresausage/Open-Source-PC110/optical/Chip Diagnostic/BRDTR.JPG

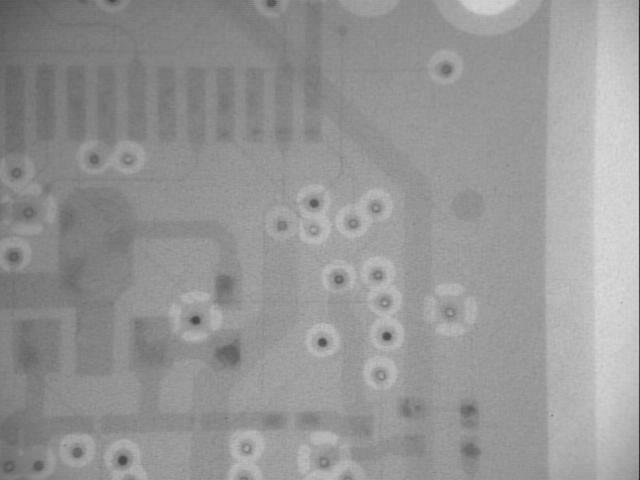
optical/Chip Diagnostic/BRDTR.JPG
