squaresausage/Open-Source-PC110/optical/Chip Diagnostic/F65535 C.JPG

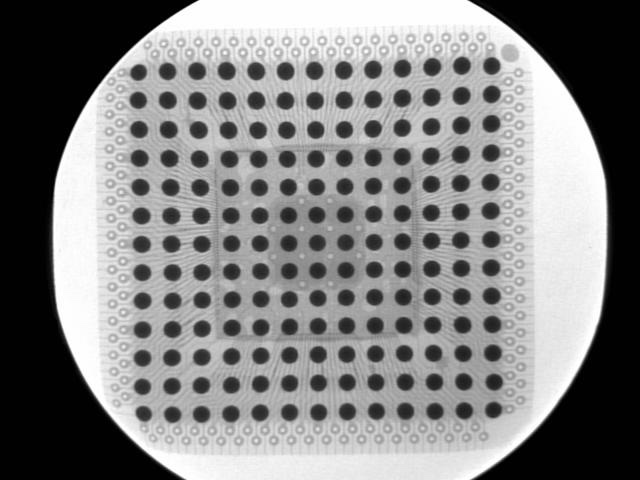
optical/Chip Diagnostic/F65535 C.JPG
