squaresausage/Open-Source-PC110/optical/Chip Diagnostic/F65535 L.JPG

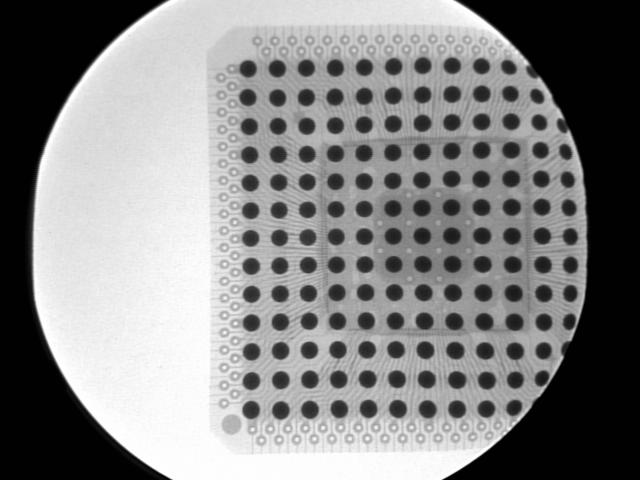
optical/Chip Diagnostic/F65535 L.JPG
