squaresausage/Open-Source-PC110/optical/Chip Diagnostic/F65535 R.JPG

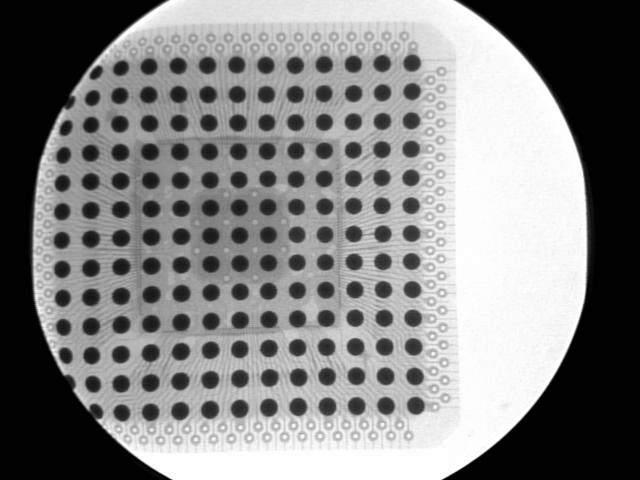
optical/Chip Diagnostic/F65535 R.JPG
