squaresausage/Open-Source-PC110/optical/Chip Diagnostic/Pluto.JPG

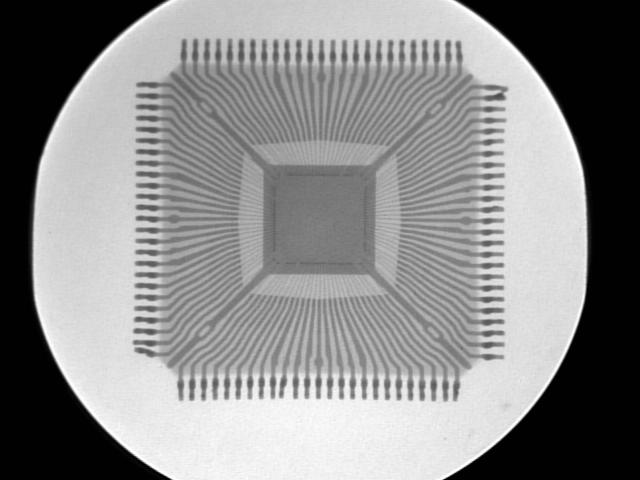
optical/Chip Diagnostic/Pluto.JPG
