squaresausage/Open-Source-PC110/optical/Chip Diagnostic/VL82C420 TL.JPG

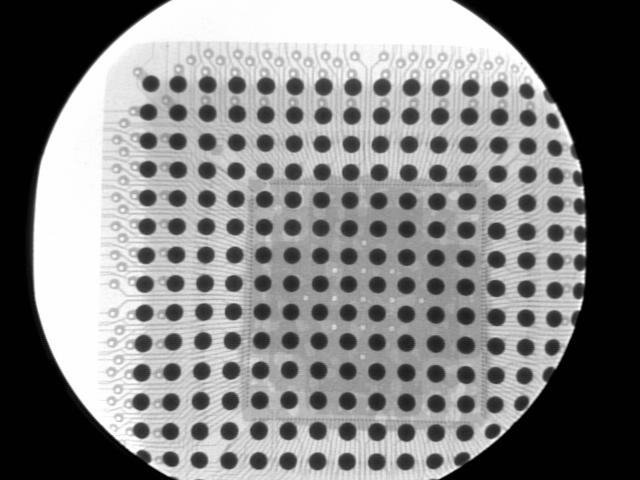
optical/Chip Diagnostic/VL82C420 TL.JPG
