squaresausage/Open-Source-PC110/optical/Chip Diagnostic/VL82C420 TR.JPG

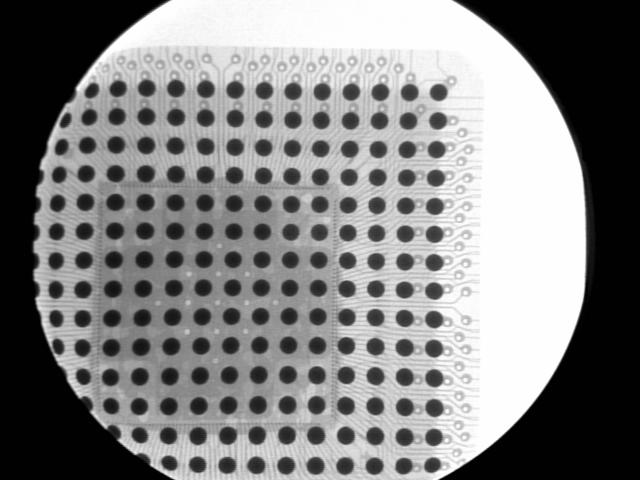
optical/Chip Diagnostic/VL82C420 TR.JPG
