squaresausage/Open-Source-PC110/optical/Chip Diagnostic/VL82C420.JPG

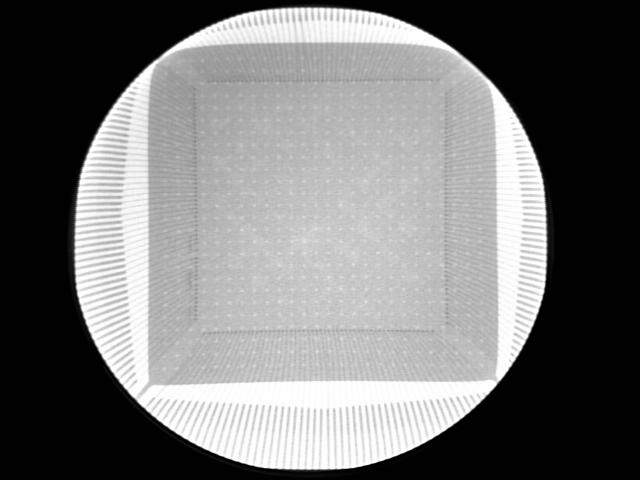
optical/Chip Diagnostic/VL82C420.JPG
