squaresausage/Open-Source-PC110/optical/DockingStation/Dock_BC_before.png

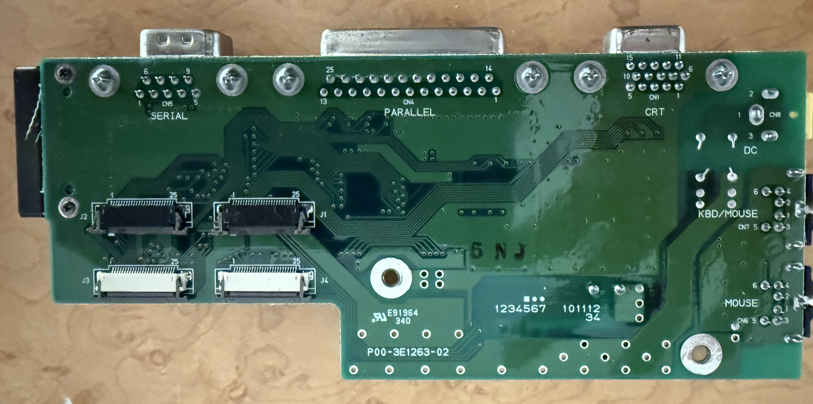
optical/DockingStation/Dock_BC_before.png
