squaresausage/Open-Source-PC110/optical/DockingStation/Dock_L68.png

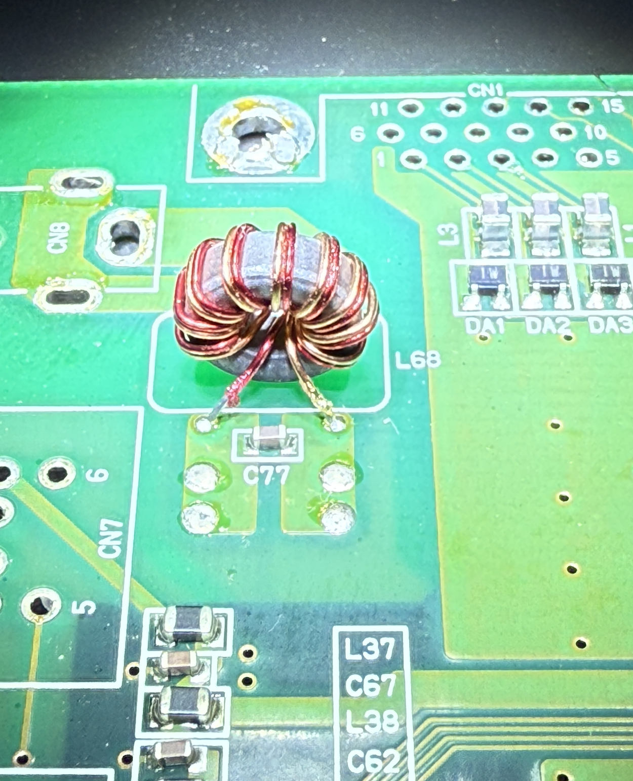
optical/DockingStation/Dock_L68.png
