squaresausage/Open-Source-PC110/optical/layers/FC2.png

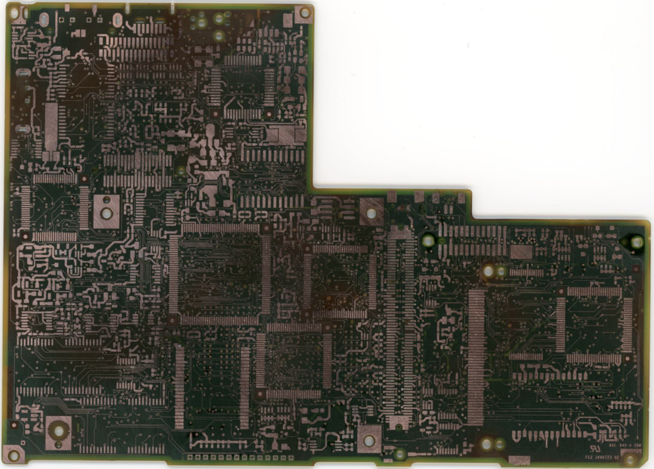
optical/layers/FC2.png
