squaresausage/Open-Source-PC110/optical/layers/IC4.png

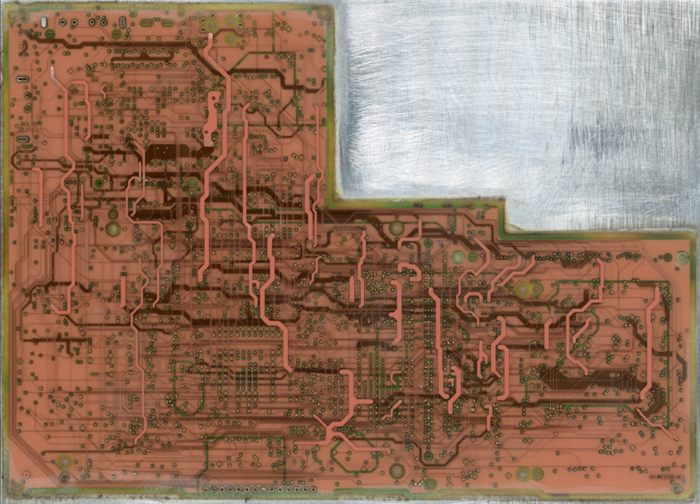
optical/layers/IC4.png
