squaresausage/Open-Source-PC110/optical/PC110 keyboard.png

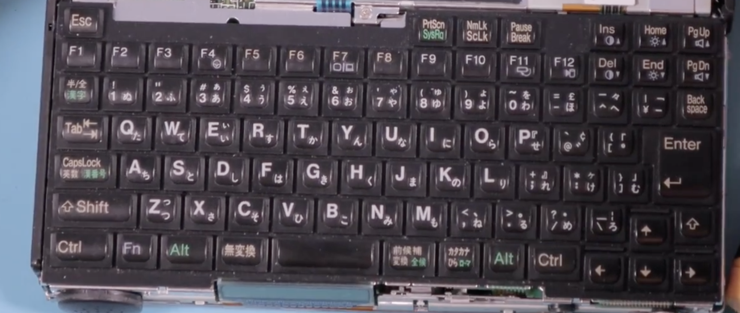
optical/PC110 keyboard.png
