squaresausage/Open-Source-PC110/optical/Pluto/Picture1.png

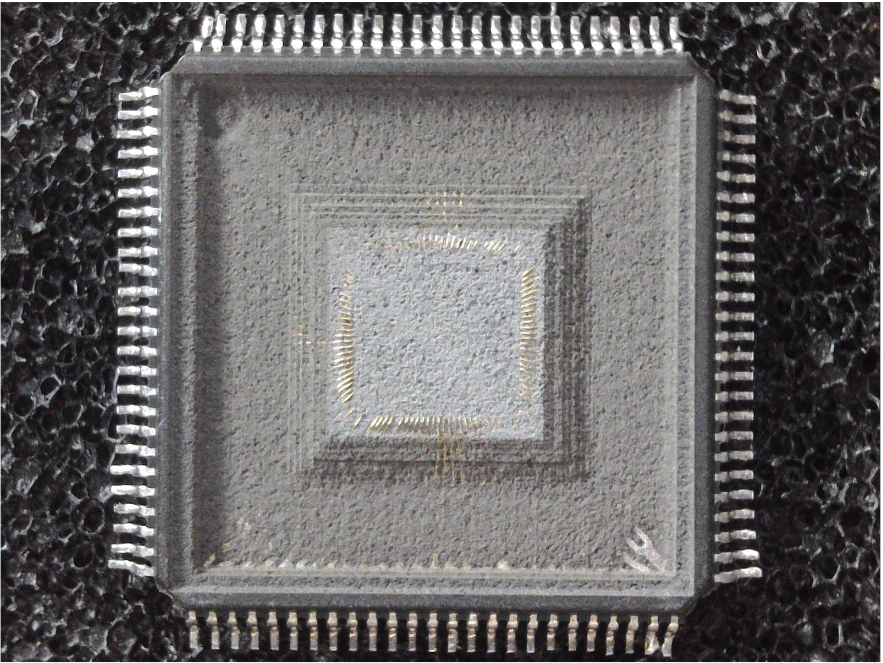
optical/Pluto/Picture1.png
