squaresausage/Open-Source-PC110/optical/Pluto/Picture2.png

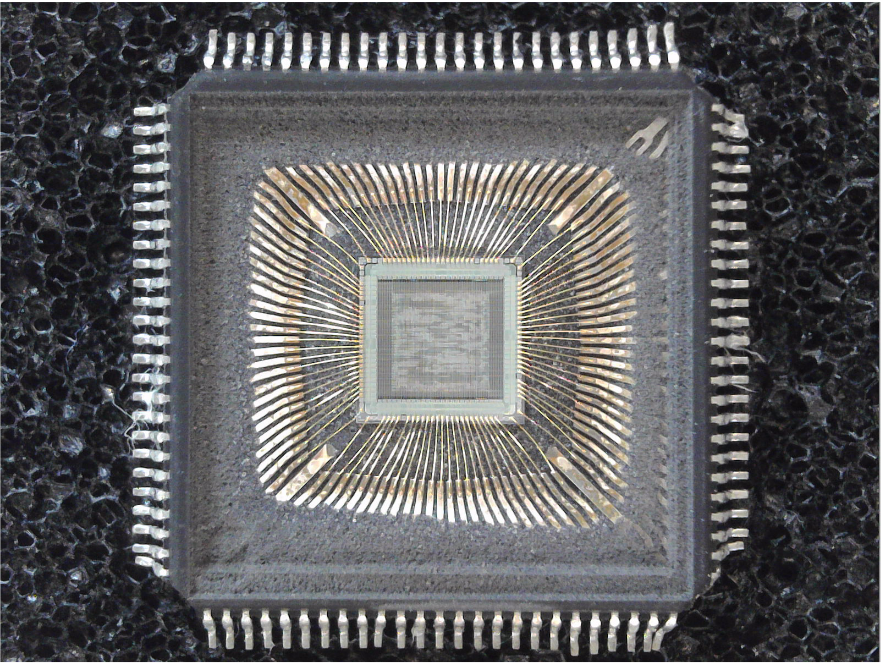
optical/Pluto/Picture2.png
