squaresausage/Open-Source-PC110/optical/Pluto/Picture3.png

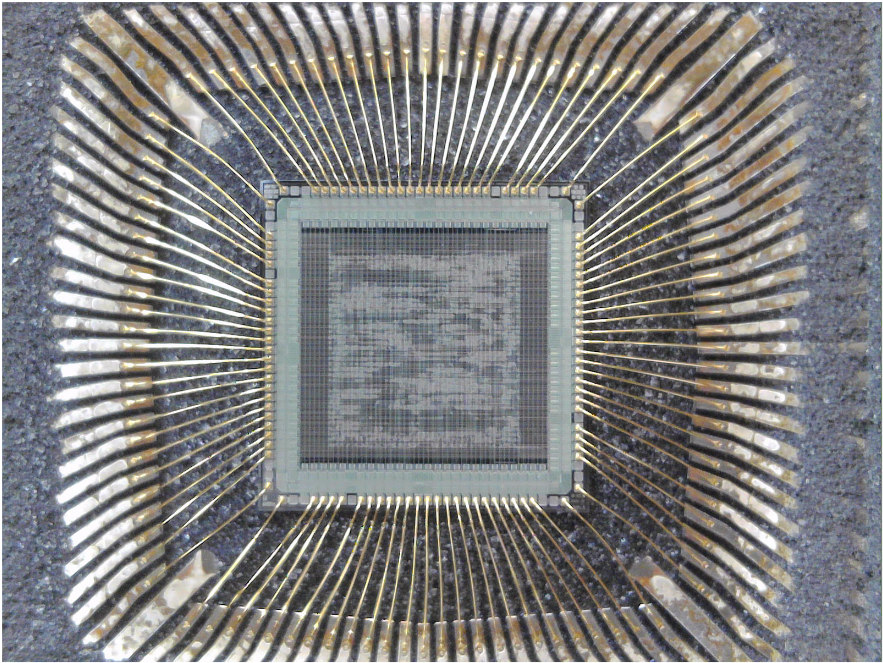
optical/Pluto/Picture3.png
