squaresausage/Open-Source-PC110/optical/Pluto/Picture4.png

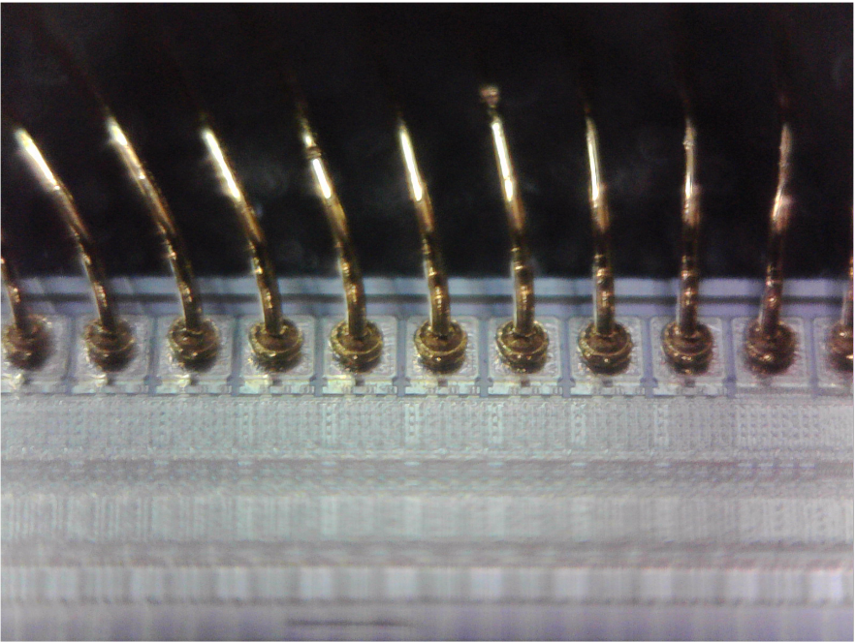
optical/Pluto/Picture4.png
