squaresausage/Open-Source-PC110/optical/Pluto/Picture5.png

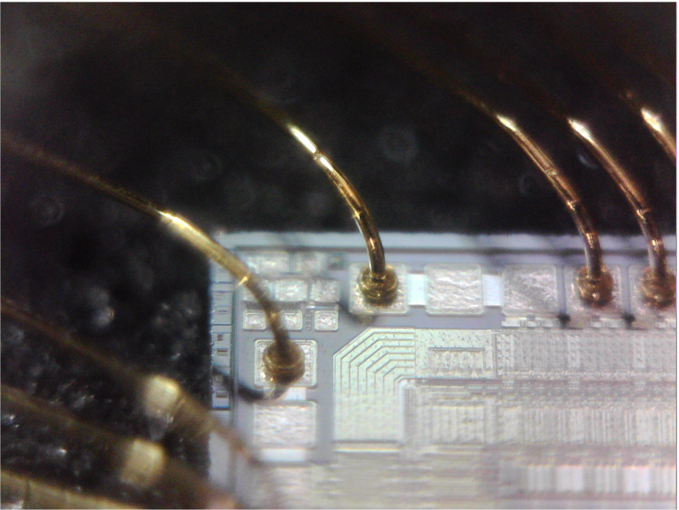
optical/Pluto/Picture5.png
