squaresausage/Open-Source-PC110/optical/Pluto/Picture6.png

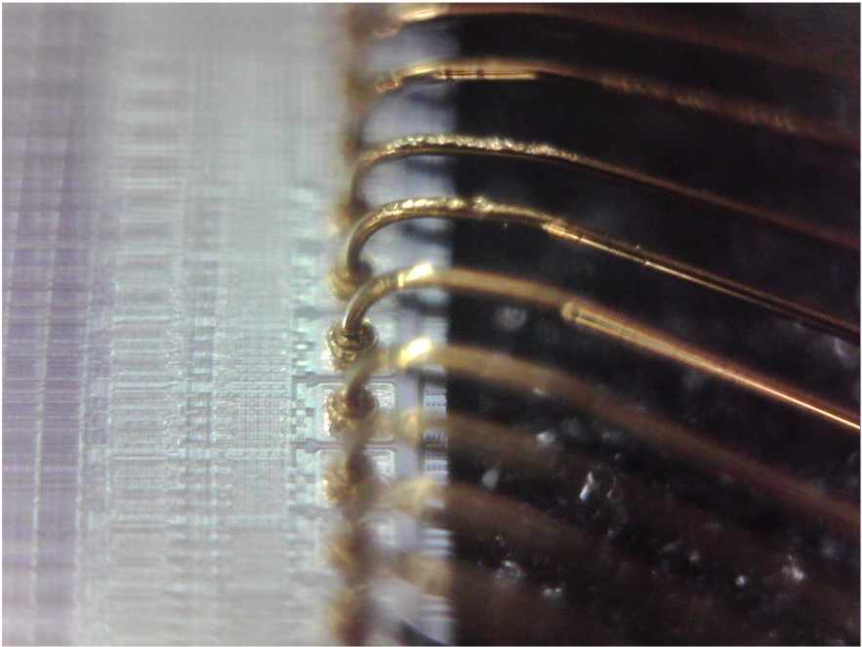
optical/Pluto/Picture6.png
