squaresausage/Open-Source-PC110/optical/Pluto/Picture7.png

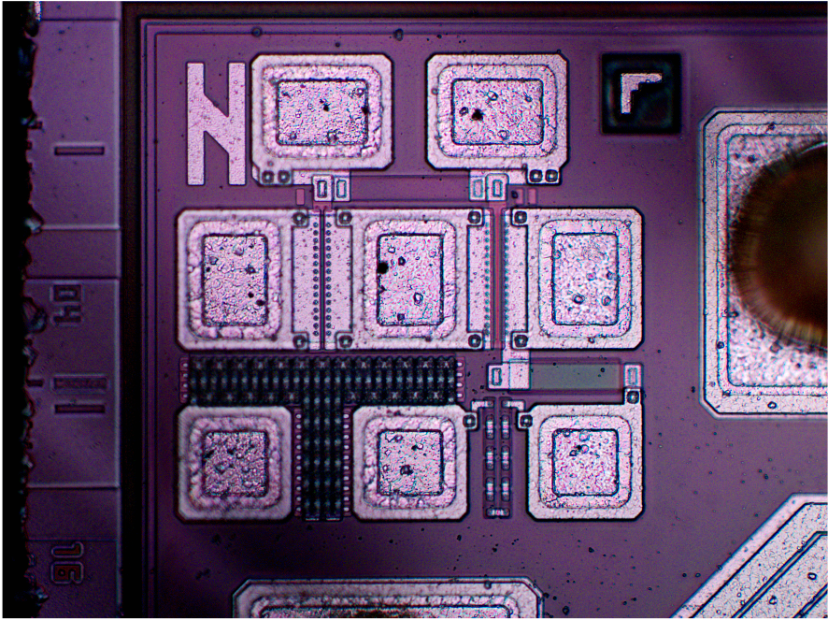
optical/Pluto/Picture7.png
