squaresausage/Open-Source-PC110/optical/Pluto/Picture8.png

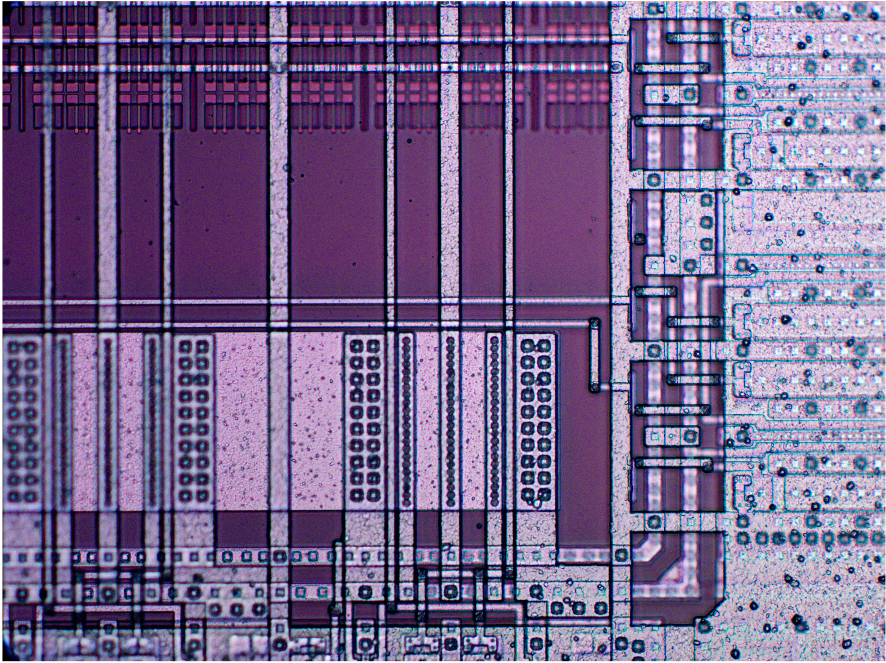
optical/Pluto/Picture8.png
