squaresausage/Open-Source-PC110/optical/Pluto/Picture10.png

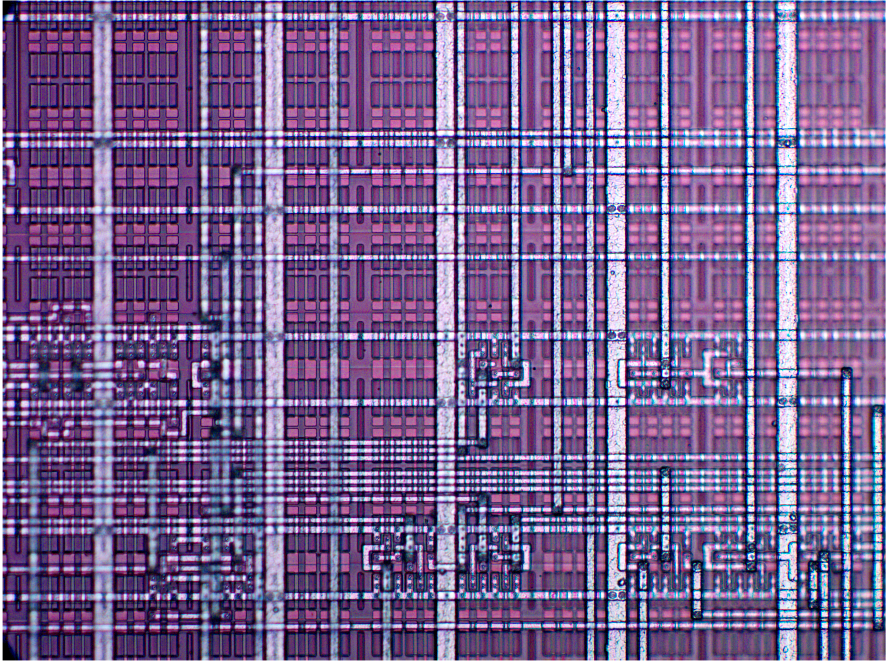
optical/Pluto/Picture10.png
