squaresausage/Open-Source-PC110/optical/Pluto/Picture12.png

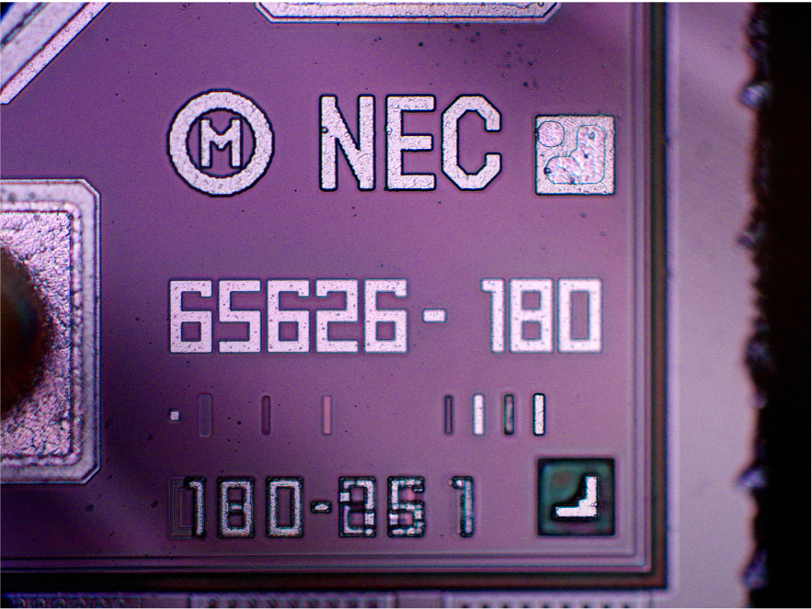
optical/Pluto/Picture12.png
