squaresausage/Open-Source-PC110/optical/VL82C420FC5/Picture1.png

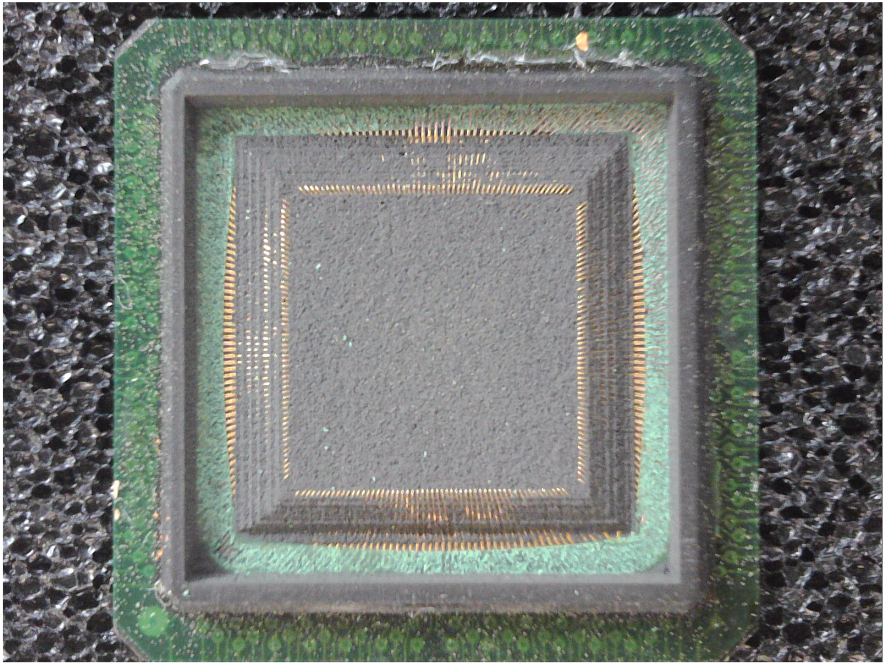
optical/VL82C420FC5/Picture1.png
