squaresausage/Open-Source-PC110/optical/VL82C420FC5/Picture2.png

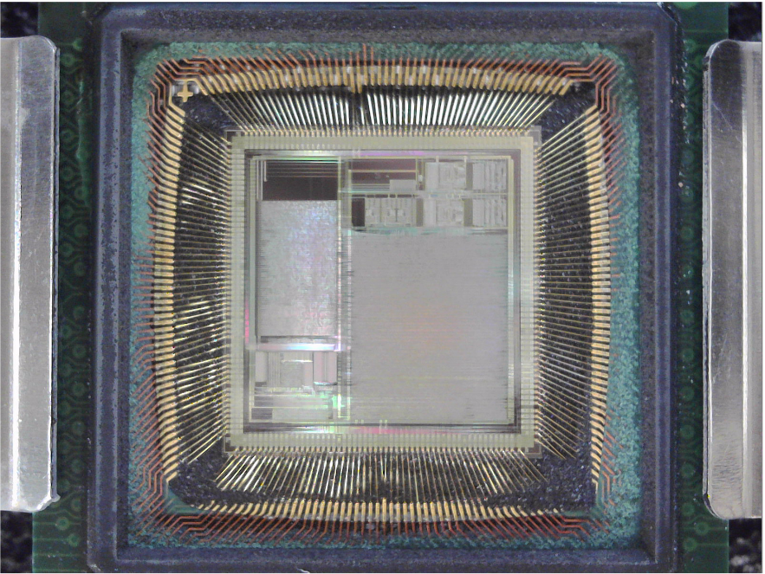
optical/VL82C420FC5/Picture2.png
