squaresausage/Open-Source-PC110/optical/VL82C420FC5/Picture5.png

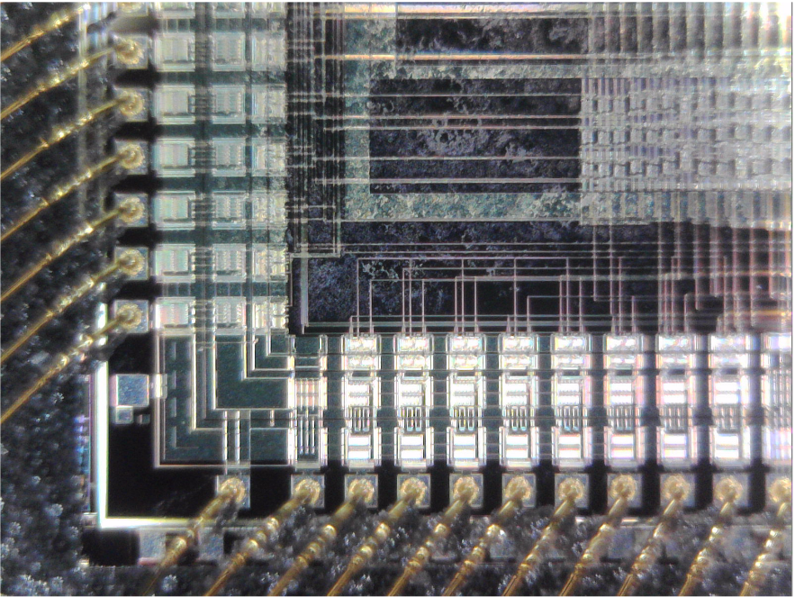
optical/VL82C420FC5/Picture5.png
