squaresausage/Open-Source-PC110/optical/VL82C420FC5/Picture7.jpg

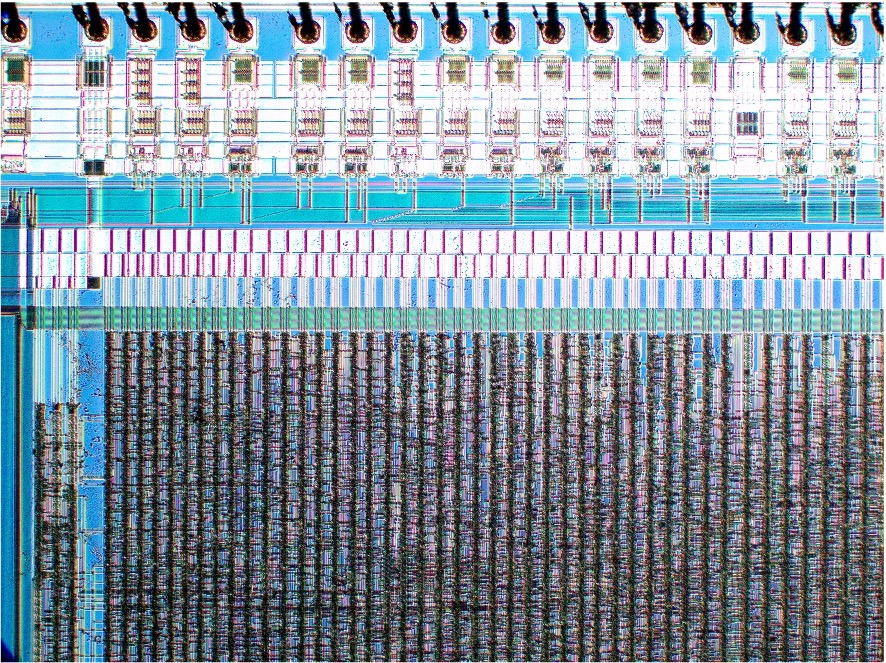
optical/VL82C420FC5/Picture7.jpg
