squaresausage/Open-Source-PC110/optical/VL82C420FC5/Picture9.jpg

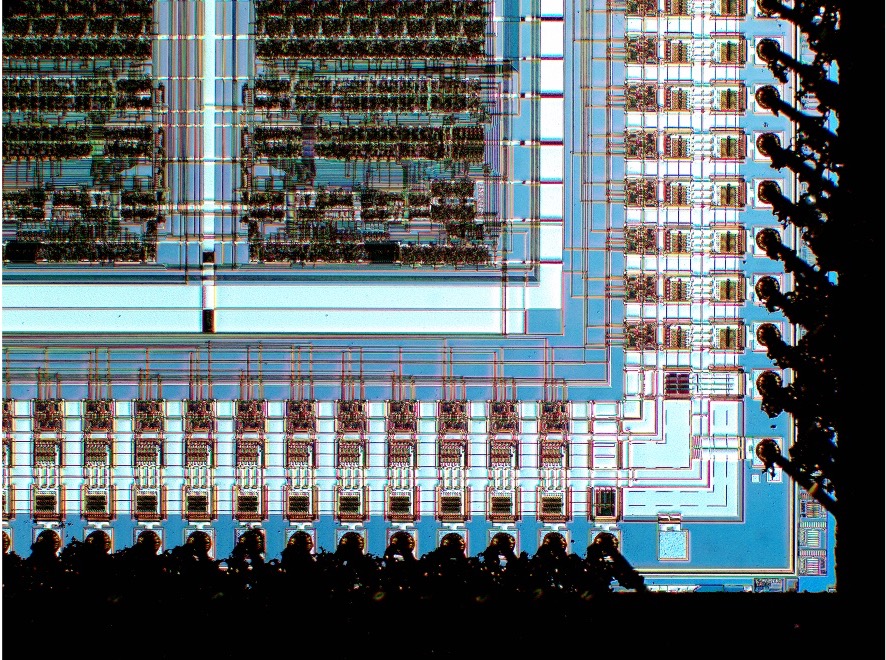
optical/VL82C420FC5/Picture9.jpg
