squaresausage/Open-Source-PC110/optical/VL82C420FC5/Picture10.jpg

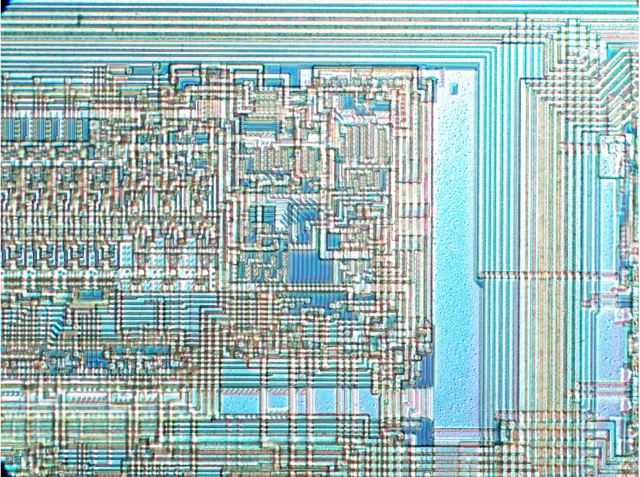
optical/VL82C420FC5/Picture10.jpg
