squaresausage/Open-Source-PC110/optical/VL82C420FC5/Picture12.jpg

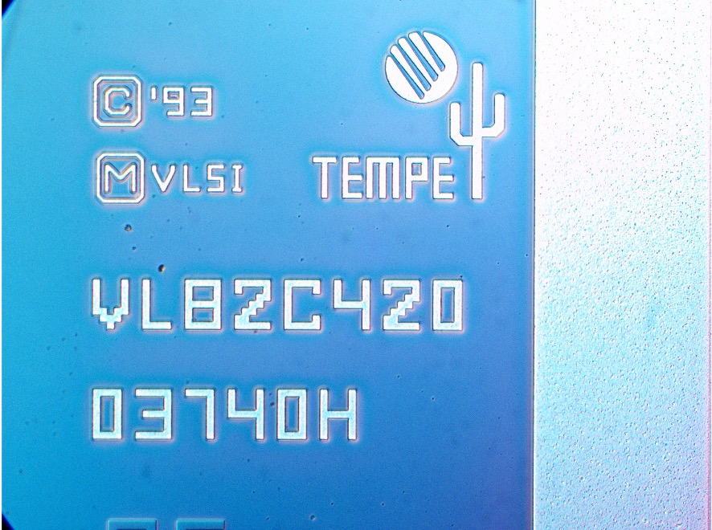
optical/VL82C420FC5/Picture12.jpg
