squaresausage/Open-Source-PC110/optical/x-ray/82c144.png

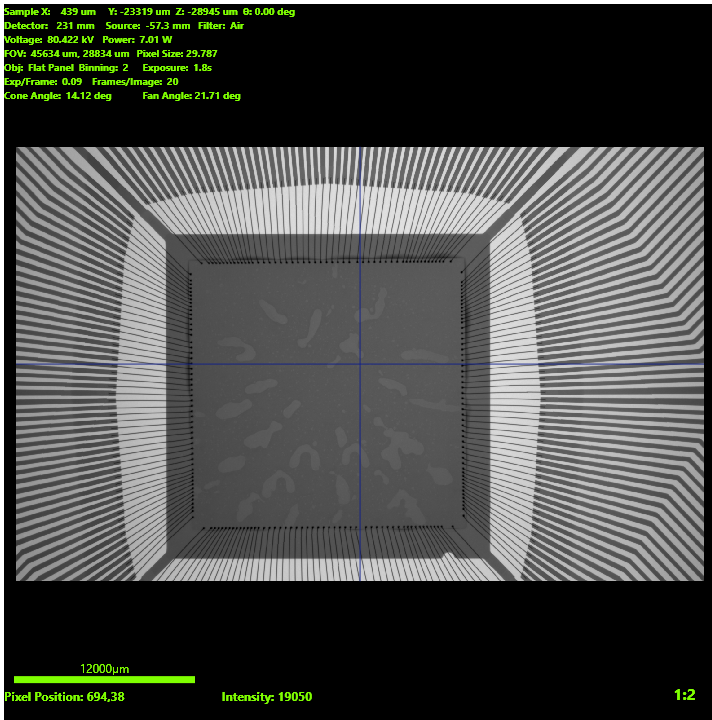
optical/x-ray/82c144.png
