squaresausage/Open-Source-PC110/optical/x-ray/82C420bga_overall.png

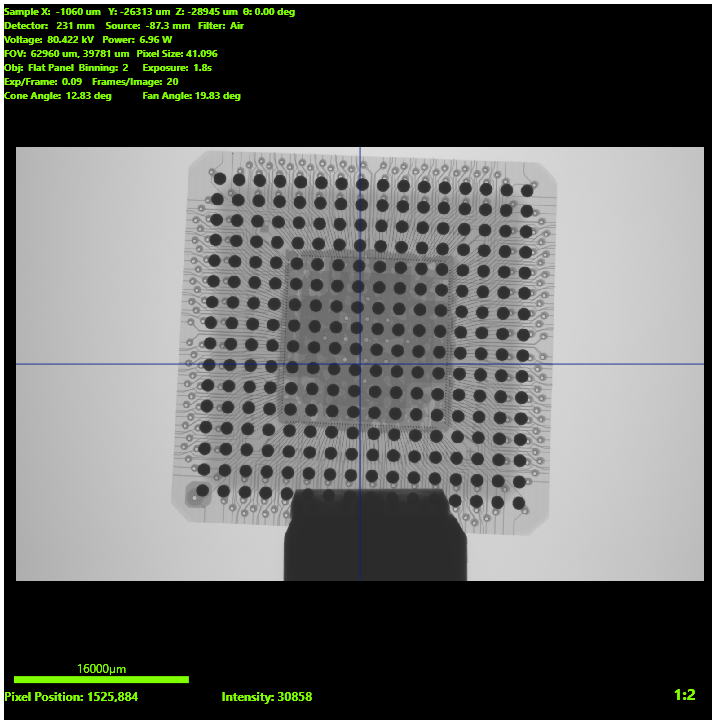
optical/x-ray/82C420bga_overall.png
