squaresausage/Open-Source-PC110/optical/x-ray/82C420qfn_overall2.png

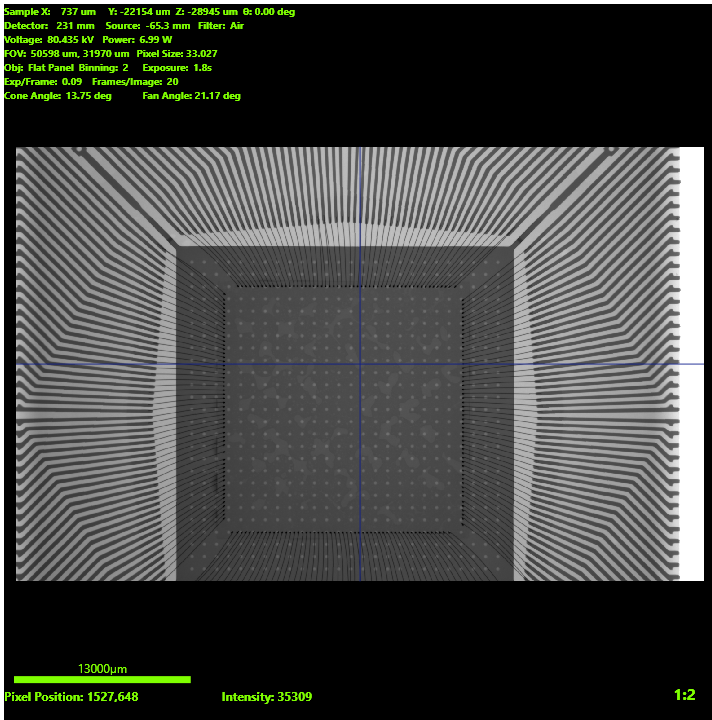
optical/x-ray/82C420qfn_overall2.png
