squaresausage/Open-Source-PC110/optical/x-ray/486.png

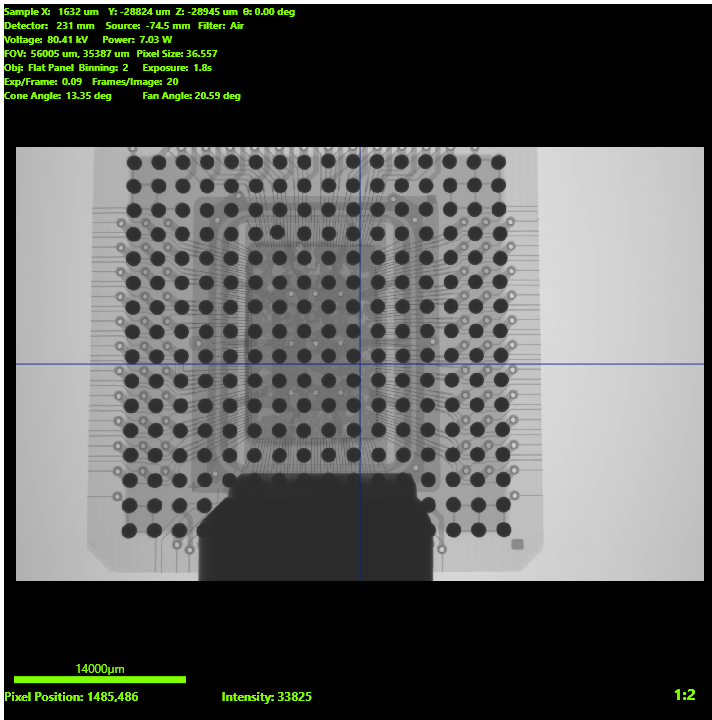
optical/x-ray/486.png
