squaresausage/Open-Source-PC110/optical/x-ray/bowman.png

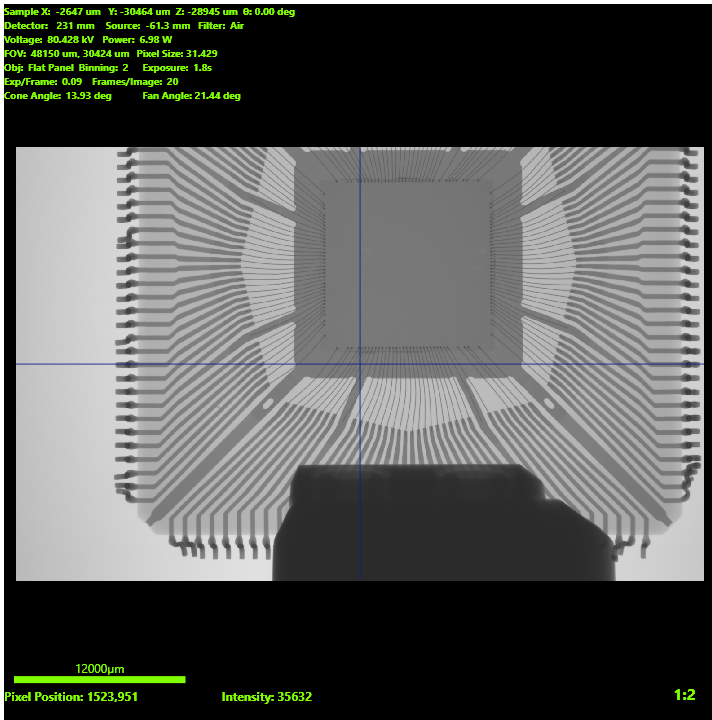
optical/x-ray/bowman.png
