squaresausage/Open-Source-PC110/Components/U61-VL82C420FC5/Interposer/README.md

## Here is the recreased BGA interposer used for the VL82C420 in the PC110

Screenshot 2025-06-20 at 10 16 22 AM

Screenshot 2025-06-20 at 10 16 29 AM
