squaresausage/Open-Source-PC110/Components/U61-VL82C420FC5/Interposer/interposer/scans/README.md

## all the scans used to recreated the interposer
Screenshot 2025-06-19 at 7 32 08 PM
Screenshot 2025-06-19 at 6 28 58 PM
Screenshot 2025-06-19 at 4 44 20 PM
Screenshot 2025-06-19 at 3 10 45 PM
Screenshot 2025-06-19 at 3 01 34 PM
