squaresausage/Open-Source-PC110/Components/U61-VL82C420FC5/Interposer/interposer/scans/82C420bga_overall.png

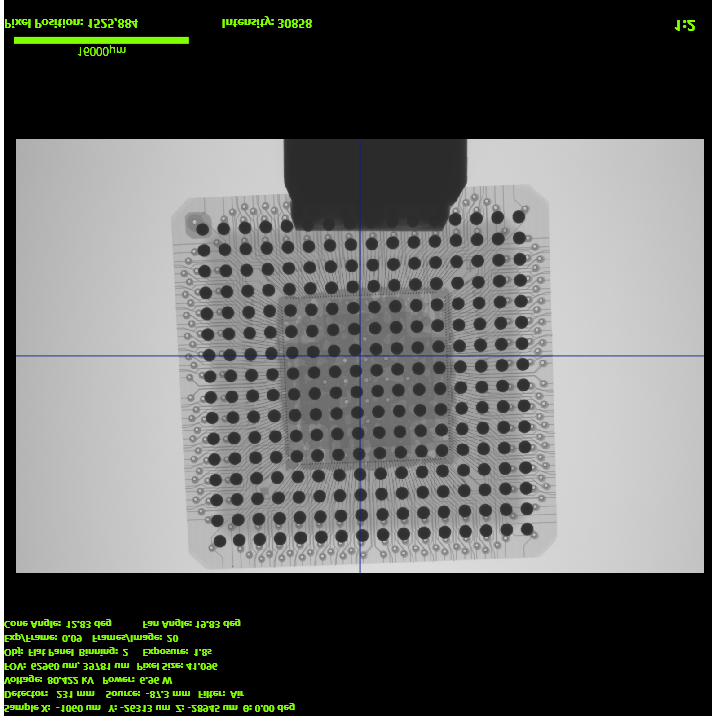
Components/U61-VL82C420FC5/Interposer/interposer/scans/82C420bga_overall.png
