squaresausage/Open-Source-PC110/Components/U61-VL82C420FC5/Interposer/interposer/scans/InterposeTop.jpg

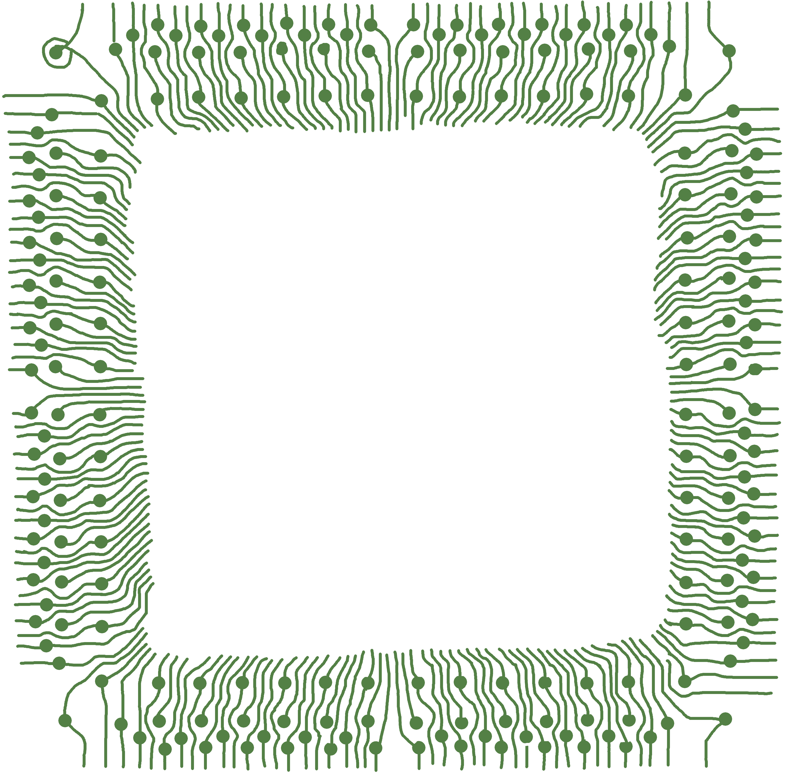
Components/U61-VL82C420FC5/Interposer/interposer/scans/InterposeTop.jpg
