squaresausage/Open-Source-PC110/Components/U61-VL82C420FC5/Interposer/interposer/scans/Photo_2025-06-19_191844.png

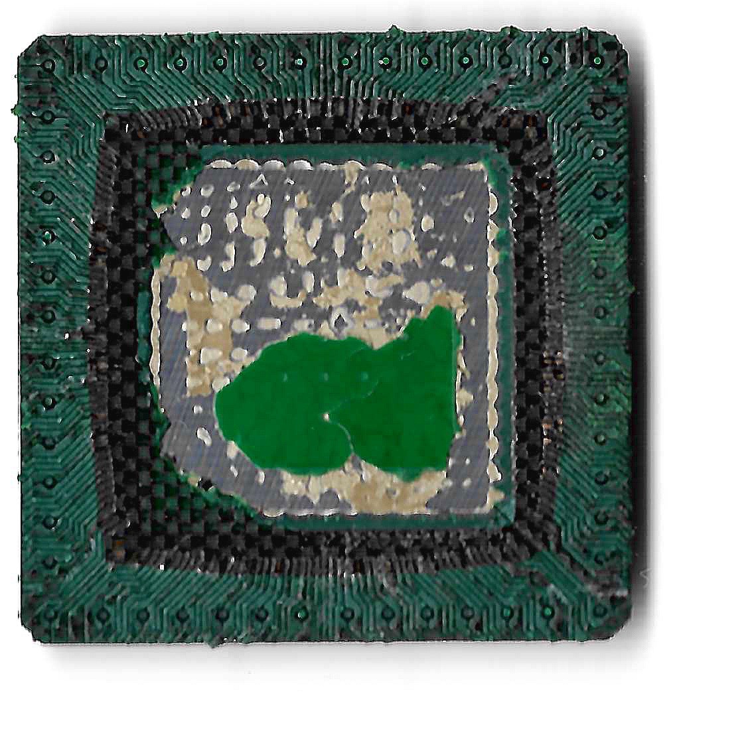
Components/U61-VL82C420FC5/Interposer/interposer/scans/Photo_2025-06-19_191844.png
