squaresausage/Open-Source-PC110/Components/U67-M38813E4HP/M38813M4.png

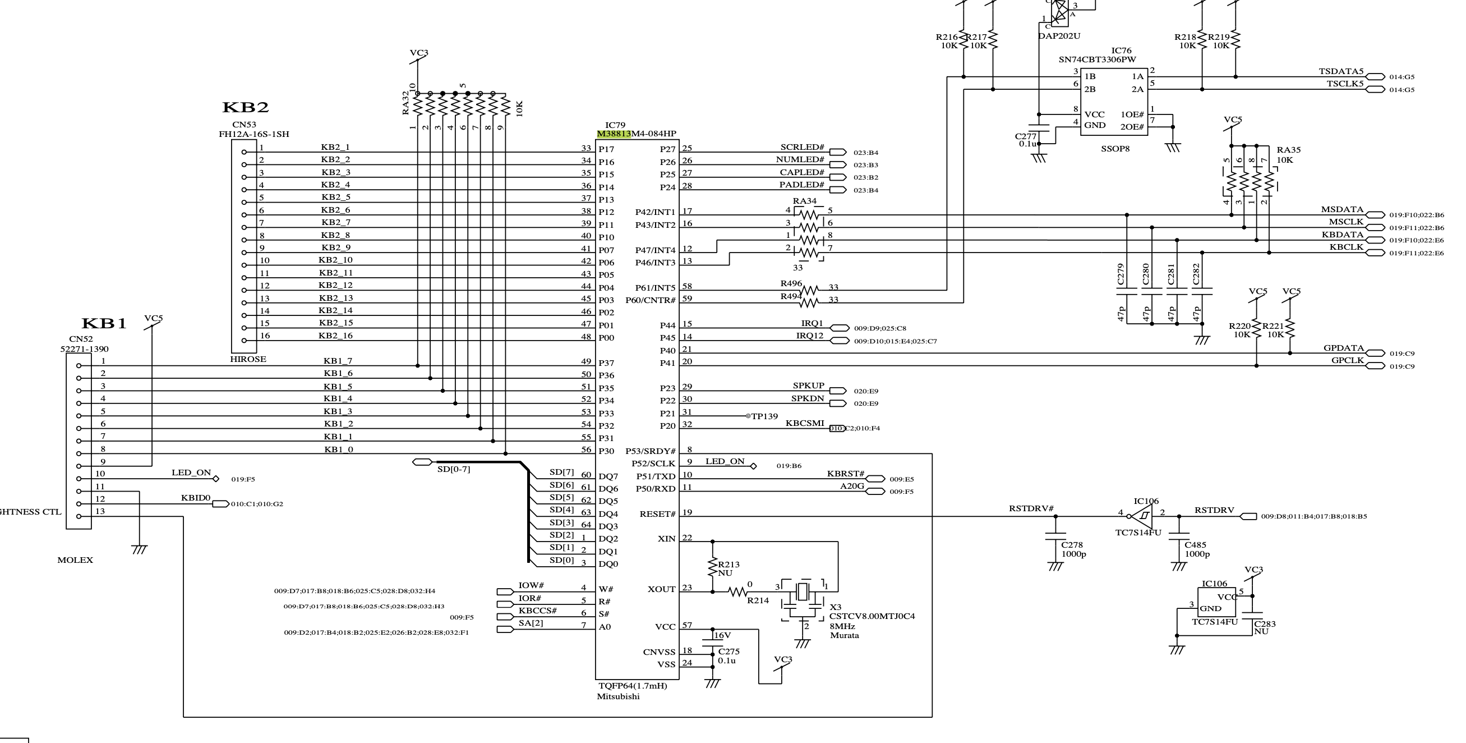
Components/U67-M38813E4HP/M38813M4.png
