squaresausage/Open-Source-PC110/optical/DockingStation/Dock_FC_Parts.png

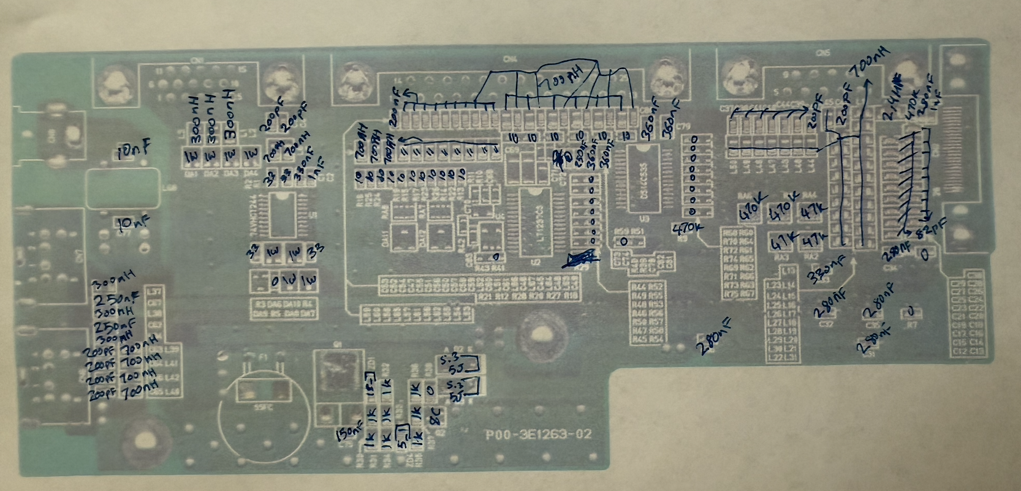
optical/DockingStation/Dock_FC_Parts.png
