squaresausage/Open-Source-PC110/optical/PSU/PSU_BC_parts.jpg

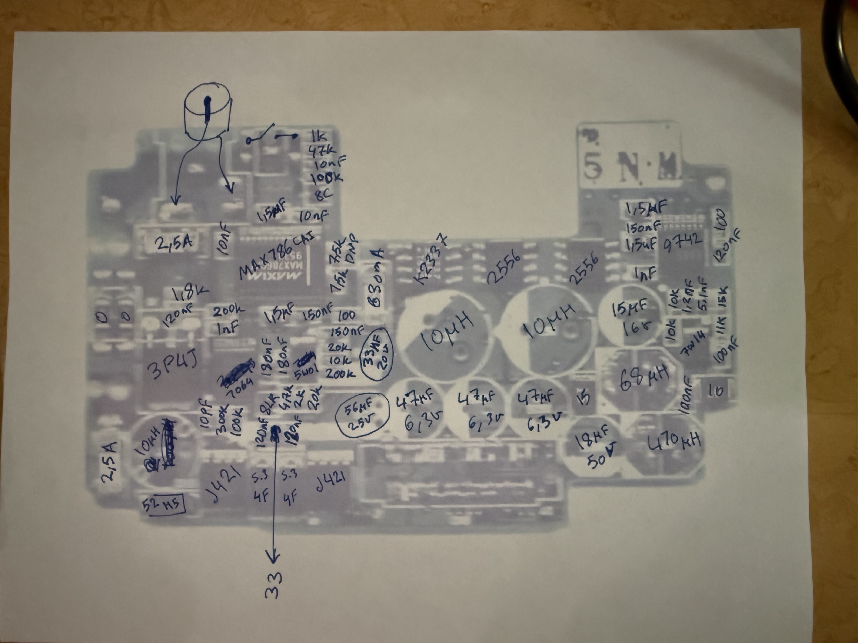
optical/PSU/PSU_BC_parts.jpg
