squaresausage/Open-Source-PC110/Components/U6-M38224M6HP/Disassembly/SquareSausage_vs_yyzkevin_rips.png

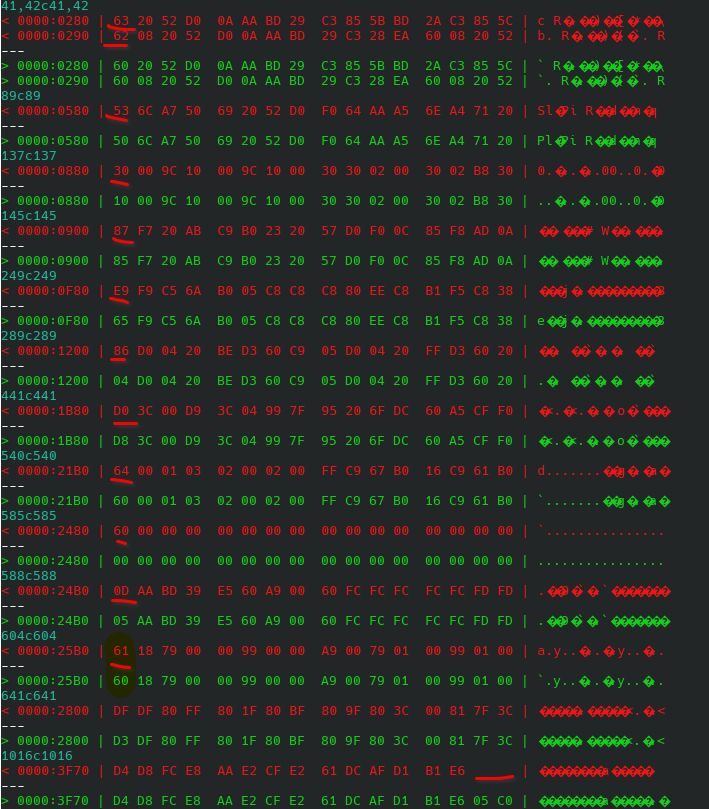
Components/U6-M38224M6HP/Disassembly/SquareSausage_vs_yyzkevin_rips.png
